jacobl423/F91_Jepler/.agents/teamwork/challenger_m1_1/progress.md

# Progress — Challenger M1-1

Last visited: 2026-10-05T20:36:00Z
Status: Empirical challenge complete. Critical bug identified and reproduced. Verdict: REJECT.

## Completed Milestones & Actions
1. Read ORIGINAL_REQUEST.md, PROJECT.md, DISPATCH.md, and worker_m1/handoff.md.
2. Verified clean build of `Software/macOS_App` with `swift build`.
3. Created empirical stress test harness (`Software/macOS_App/scripts/empirical_challenger_harness.swift`).
4. Verified valid repository binaries (`app.signed.bin`, `mcuboot.elf`, `f91_jepler.resc`, `f91_jepler.kicad_pcb`, `blaster_6810.hex`).
5. Verified 0-byte empty files, corrupted MCUboot headers, corrupted ELF headers, corrupted KiCad PCB S-expressions, directory handling, permissions, and concurrency.
6. Empirically discovered and confirmed CRITICAL SIGTRAP crash (`Fatal error: String index is out of bounds`) in `AssetInspector.swift:344` and `AssetInspector.swift:350` when parsing adversarial pseudo-hex lines with record types 04 and 05.
7. Confirmed that persistent `UserDefaults` state triggers an unrecoverable crash loop on startup.
8. Authored comprehensive adversarial challenge report and handoff in `handoff.md`.
