jacobl423/F91_Jepler/.agents/teamwork/challenger_m2_2/progress.md

# Progress — Challenger M2-2

Last visited: 2026-10-05T21:40:20Z

## Current Status
- Created and executed empirical test harness: `Software/macOS_App/scripts/empirical_challenger_m2_2_harness.swift`.
- Tested 45 empirical test cases across 5 test suites:
  1. Suite 1: Sidebar Visibility Persistence & Dual-Key Synchronization (6 tests, 3 failed)
  2. Suite 2: Sidebar Width Bounds & Clamping 230..380 (8 tests, 4 failed)
  3. Suite 3: Asset Revert Safety (3 tests, all passed)
  4. Suite 4: Non-Modal Action Safety (6 tests, all passed)
  5. Suite 5: ViewMode & Multi-Launch Simulated Cycles (10 tests, all passed)
- Overall Empirical Results: 38 Passed, 7 Failed.
- Final Verdict: REJECT.
- Next: Update BRIEFING.md and write handoff.md.
