jacobl423/F91_Jepler/.agents/teamwork/explorer_m1_1/BRIEFING.md

# BRIEFING — 2026-10-05T20:15:15Z

## Mission
Investigate and specify SessionAsset.swift and AssetInspector.swift for Milestone 1 of the F91_Jepler macOS companion app.

## 🔒 My Identity
- Archetype: explorer
- Roles: Asset Model & Inspector Explorer
- Working directory: /Users/jacobloesch/Documents/F91_Jepler/.agents/teamwork/explorer_m1_1
- Original parent: 6b5ed2d8-2b1d-40f1-8ab6-ad53a69017cd
- Milestone: M1 (Asset Models, Metadata Engine & Session Integration)

## 🔒 Key Constraints
- Read-only investigation — do NOT implement
- Do not modify source code in Software/macOS_App
- Write findings and handoff report to /Users/jacobloesch/Documents/F91_Jepler/.agents/teamwork/explorer_m1_1/handoff.md
- Adhere to Swift 5/6 concurrency, Sendable, @MainActor conventions for macOS 13+

## Current Parent
- Conversation ID: 6b5ed2d8-2b1d-40f1-8ab6-ad53a69017cd
- Updated: not yet

## Investigation State
- **Explored paths**:
  - `ORIGINAL_REQUEST.md`, `PROJECT.md`, `DISPATCH.md`
  - `Software/macOS_App/Package.swift` (macOS 13+, Swift 5.9 tools version)
  - `Software/macOS_App/F91JeplerEmulator/Models/EmulatorSession.swift`
  - `Software/macOS_App/F91JeplerEmulator/Engine/ResourceLoader.swift`
  - `Software/macOS_App/F91JeplerEmulator/Engine/RenodeScriptGenerator.swift`
  - `Software/macOS_App/F91JeplerEmulator/Engine/RenodeProcessManager.swift`
  - `Software/macOS_App/F91JeplerEmulator/Engine/KiCadParser.swift`
  - `Software/macOS_App/F91JeplerEmulator/Views/ContentView.swift`
  - Embedded sample files: `app.signed.bin`, `mcuboot.elf`, `f91_jepler.resc`, `f91_jepler.kicad_pcb`, `blaster_6810.hex`
- **Key findings**:
  - MCUboot image binary header starts with LE magic `0x96F3B83D`, image size at offset 12, semantic version at offset 20.
  - ELF32 ARM binary starts with `\x7fELF`, `EI_CLASS=1`, `EI_DATA=1`, `e_machine=0x0028` (EM_ARM Cortex-M), entry point at offset 24 (with Thumb mode bit).
  - Intel HEX records start with `:`, but Renode `.resc` scripts also have headers `:name:` and `:description:`. Disambiguation requires verifying that payload characters are exclusively hex digits `[0-9a-fA-F]` and record types are `0x00...0x05`.
  - KiCad PCB S-expression starts with `(kicad_pcb`, with regex extraction for `version`, `generator`, and `thickness`.
  - Dynamic binary loading requires generating `sysbus LoadELF`, `sysbus LoadHEX`, or `sysbus LoadBinary ... 0x0c000` based on file extension, and preserving staged file extensions in `RenodeProcessManager`.
  - Hot in-memory PCB reloading updates `pcbBoard` and restarts `pcbFileWatcher` without stopping the running Renode process.
  - Swift concurrency safety: `SessionAssetKind`, `AssetLoadState`, `AssetMetadata`, and `SessionAsset` conform to `Sendable`. `AssetInspector` executes asynchronous non-blocking file I/O on background cooperative threads using `Task.detached`. `EmulatorSession` runs strictly on `@MainActor`.
- **Unexplored areas**:
  - Milestone 2 UI components (`ProjectSidebarView.swift`) and toolbar button integrations (assigned to M2).

## Key Decisions Made
- Validated complete proposed implementations of `proposed_SessionAsset.swift` and `proposed_AssetInspector.swift` against all real repository binaries using native Swift compilation.
- Designed exact interface contracts and backward-compatibility bindings for `EmulatorSession`, `RenodeScriptGenerator`, and `RenodeProcessManager`.

## Artifact Index
- `DISPATCH.md` — Initial dispatch instructions & incoming message log
- `BRIEFING.md` — Working memory state
- `progress.md` — Liveness heartbeat
- `proposed_SessionAsset.swift` — Turnkey Swift model code for `SessionAsset.swift`
- `proposed_AssetInspector.swift` — Turnkey Swift engine code for `AssetInspector.swift`
- `proposed_EmulatorSession_integration.md` — Integration specification and code for `EmulatorSession.swift`
- `proposed_Renode_Binary_Loading.md` — Dynamic binary loading spec for `RenodeScriptGenerator.swift` and `RenodeProcessManager.swift`
- `handoff.md` — Authoritative 5-component handoff report
