jacobl423/F91_Jepler/.agents/teamwork/explorer_m1_1/DISPATCH.md

# Dispatch for Explorer M1_1

## Identity
- Role: Asset Model & Inspector Explorer
- Type: teamwork_preview_explorer
- Working directory: /Users/jacobloesch/Documents/F91_Jepler/.agents/teamwork/explorer_m1_1
- Parent Orchestrator: /Users/jacobloesch/Documents/F91_Jepler/.agents/teamwork/orchestrator_macos
- Authoritative User Request: /Users/jacobloesch/Documents/F91_Jepler/.agents/teamwork/ORIGINAL_REQUEST.md
- Project Scope Document: /Users/jacobloesch/Documents/F91_Jepler/.agents/teamwork/orchestrator_macos/PROJECT.md

## Milestone Scope: M1 - Asset Models & Metadata Engine
Analyze the detailed implementation requirements for:
1. `SessionAsset.swift`: Design `SessionAssetKind` (`.pcb`, `.appFirmware`, `.bootloader`, `.rescScript`), `AssetLoadState`, `AssetMetadata`, and `SessionAsset`.
2. `AssetInspector.swift`: Asynchronous metadata extractor capable of parsing file sizes, modification dates, and binary magic bytes (MCUboot image magic `0x96F3B83D`, ELF32 ARM Cortex-M header `0x7F 'E' 'L' 'F'`, Intel HEX, KiCad S-expression).
3. Recommend exact type signatures, Swift concurrency safety (@MainActor / Sendable), and file structure for `Software/macOS_App/F91JeplerEmulator/Models/SessionAsset.swift` and `Software/macOS_App/F91JeplerEmulator/Engine/AssetInspector.swift`.
4. Write your comprehensive analysis and implementation recommendation to `/Users/jacobloesch/Documents/F91_Jepler/.agents/teamwork/explorer_m1_1/handoff.md`.

## 2026-10-05T20:07:15Z
You are the Asset Model & Inspector Explorer for Milestone 1 of the F91_Jepler project. Your working directory is /Users/jacobloesch/Documents/F91_Jepler/.agents/teamwork/explorer_m1_1. Read /Users/jacobloesch/Documents/F91_Jepler/.agents/teamwork/ORIGINAL_REQUEST.md, /Users/jacobloesch/Documents/F91_Jepler/.agents/teamwork/orchestrator_macos/PROJECT.md, and /Users/jacobloesch/Documents/F91_Jepler/.agents/teamwork/explorer_m1_1/DISPATCH.md before starting work. Investigate and design the exact specifications for SessionAsset.swift and AssetInspector.swift in Software/macOS_App, including SessionAssetKind, AssetLoadState, AssetMetadata, header magic extraction (MCUboot, ELF ARM Cortex-M, Intel HEX, KiCad S-expr), and thread safety. Write your handoff report to /Users/jacobloesch/Documents/F91_Jepler/.agents/teamwork/explorer_m1_1/handoff.md and report back when complete.
