jacobl423/F91_Jepler/.agents/teamwork/explorer_m1_1/progress.md

# Progress — explorer_m1_1

Last visited: 2026-10-05T20:15:25Z
Current status: Completed investigation, validated models against real files, and prepared 5-component handoff report.

## Steps
- [x] Received dispatch message and initialized BRIEFING.md and DISPATCH.md
- [x] Inspect existing `Software/macOS_App` directory layout and files
- [x] Examine `Package.swift` and compiler/target configuration
- [x] Examine existing `EmulatorSession.swift`, `RenodeScriptGenerator.swift`, `KiCadPcbParser.swift`, etc.
- [x] Investigate header magic formats:
  - MCUboot image header structure and magic (`0x96F3B83D`, version, load address, image size)
  - ELF32 header (ident `\x7fELF`, machine `0x28` ARM Cortex-M, entry point, 32-bit LE)
  - Intel HEX format (colon `:` records, hex character validation, address calculation)
  - KiCad PCB S-expression format (`(kicad_pcb ...)` version, generator, thickness)
  - Renode script (`:name:`, `:description:`, platforms)
- [x] Design type signatures and architecture for `SessionAsset.swift` and `AssetInspector.swift`
- [x] Verify thread safety / Swift concurrency (@MainActor vs Sendable background actor/tasks)
- [x] Compile and test proposed models against real binaries in repository
- [x] Write comprehensive handoff report to `handoff.md`
- [ ] Send completion message to parent orchestrator
