jacobl423/F91_Jepler/.agents/teamwork/explorer_m1_2/BRIEFING.md

# BRIEFING — 2026-10-05T20:14:00Z

## Mission
Investigate and design exact modifications for RenodeScriptGenerator.swift and RenodeProcessManager.swift in Software/macOS_App to dynamically support LoadELF, LoadHEX, and LoadBinary for application and bootloader binaries, preserve file extensions in staging, and verify non-blocking hot PCB reloading.

## 🔒 My Identity
- Archetype: explorer
- Roles: Renode & Process Manager Explorer, Dynamic Loading Explorer
- Working directory: /Users/jacobloesch/Documents/F91_Jepler/.agents/teamwork/explorer_m1_2
- Original parent: 6b5ed2d8-2b1d-40f1-8ab6-ad53a69017cd
- Milestone: Milestone 1 - Dynamic Renode Loading & Staging

## 🔒 Key Constraints
- Read-only investigation — do NOT implement directly in Software/macOS_App source
- Deliver structured handoff report in /Users/jacobloesch/Documents/F91_Jepler/.agents/teamwork/explorer_m1_2/handoff.md
- Use send_message to report back to parent

## Current Parent
- Conversation ID: 6b5ed2d8-2b1d-40f1-8ab6-ad53a69017cd
- Updated: not yet

## Investigation State
- **Explored paths**:
  - `Software/macOS_App/F91JeplerEmulator/Engine/RenodeScriptGenerator.swift`
  - `Software/macOS_App/F91JeplerEmulator/Engine/RenodeProcessManager.swift`
  - `Software/macOS_App/F91JeplerEmulator/Models/EmulatorSession.swift`
  - `Software/macOS_App/F91JeplerEmulator/Engine/PCBValidator.swift`
  - `Software/macOS_App/F91JeplerEmulator/Engine/PCBFileWatcher.swift`
  - `Software/macOS_App/F91JeplerEmulator/Engine/KiCadToolService.swift`
  - `Software/macOS_App/F91JeplerEmulator/Views/KiCadPcbView.swift`
  - `Software/macOS_App/F91JeplerEmulator/Resources/Embedded/f91_jepler.resc`
- **Key findings**:
  - `RenodeScriptGenerator.swift` hardcoded `sysbus LoadELF $mcuboot_bin` and `sysbus LoadBinary $app_bin 0x0c000`.
  - Added `BinaryFormat` enum (`.elf`, `.hex`, `.binary`) and `detectFormat(path:)` inspecting ELF magic (`\x7fELF`) / Intel HEX `:` with extension fallback.
  - Added dynamic load command emission: `sysbus LoadELF`, `sysbus LoadHEX`, or `sysbus LoadBinary $app_bin 0x0c000` / `$mcuboot_bin 0x00000`.
  - `RenodeProcessManager.swift` hardcoded staging destination names `app.signed.bin` and `mcuboot.elf`, discarding original file extensions and formats.
  - Redesigned staging to sanitize filenames while preserving extensions (`app.hex`, `zephyr.elf`, `mcuboot.hex`, `mcuboot.bin`, `app.signed.bin`).
  - Verified PCB hot reload in `EmulatorSession.reloadPCB(fileURL:)`: re-parses KiCad files in-memory via `KiCadParser.parseAsync`, runs 15-rule in-memory DRC via `PCBValidator.validate`, refreshes `runKiCadDRC()` if active, and alerts if GPIO pins drift via `GPIOPinAuditor`. Emulation subprocess `RenodeProcessManager` is NOT stopped or restarted; sockets and logs remain alive.
- **Unexplored areas**: Milestone 3 test target setup and test cases.

## Key Decisions Made
- Authored proposed replacement files `proposed_RenodeScriptGenerator.swift` and `proposed_RenodeProcessManager.swift`.
- Authored unified patch `renode_dynamic_loading.patch`.

## Artifact Index
- /Users/jacobloesch/Documents/F91_Jepler/.agents/teamwork/explorer_m1_2/DISPATCH.md — Dispatch instructions
- /Users/jacobloesch/Documents/F91_Jepler/.agents/teamwork/explorer_m1_2/BRIEFING.md — Persistent memory
- /Users/jacobloesch/Documents/F91_Jepler/.agents/teamwork/explorer_m1_2/progress.md — Liveness heartbeat
- /Users/jacobloesch/Documents/F91_Jepler/.agents/teamwork/explorer_m1_2/proposed_RenodeScriptGenerator.swift — Proposed script generator
- /Users/jacobloesch/Documents/F91_Jepler/.agents/teamwork/explorer_m1_2/proposed_RenodeProcessManager.swift — Proposed process manager
- /Users/jacobloesch/Documents/F91_Jepler/.agents/teamwork/explorer_m1_2/renode_dynamic_loading.patch — Unified patch
- /Users/jacobloesch/Documents/F91_Jepler/.agents/teamwork/explorer_m1_2/handoff.md — Final handoff report
