jacobl423/F91_Jepler/.agents/teamwork/explorer_m1_2/progress.md

# Progress: Explorer M1_2 (Renode Dynamic Loading & Staging)
Last visited: 2026-10-05T20:14:55Z

- [x] Initialized DISPATCH.md, BRIEFING.md, and progress.md
- [x] Read ORIGINAL_REQUEST.md and orchestrator_macos/PROJECT.md
- [x] Inspect existing RenodeScriptGenerator.swift and RenodeProcessManager.swift
- [x] Inspect PCB hot reloading in EmulatorSession, KiCadParser, PCBValidator, KiCadToolService, and KiCadPcbView
- [x] Verify non-blocking subprocess independence of PCB reload
- [x] Design exact modifications and diff strategy
- [x] Authored proposed_RenodeScriptGenerator.swift
- [x] Authored proposed_RenodeProcessManager.swift
- [x] Authored renode_dynamic_loading.patch
- [x] Formulate handoff report to handoff.md
- [x] Send completion message to orchestrator
