jacobl423/F91_Jepler/.agents/teamwork/explorer_survey_2_rep/BRIEFING.md

# BRIEFING — 2026-10-05T20:05:00Z

## Mission
Investigate Software/macOS_App asset models, emulator session configurations, file loaders, metadata extraction, quick actions, UTTypes, and session integration for the collapsible sidebar redesign.

## 🔒 My Identity
- Archetype: explorer
- Roles: Asset & Session Explorer
- Working directory: /Users/jacobloesch/Documents/F91_Jepler/.agents/teamwork/explorer_survey_2_rep
- Original parent: 6b5ed2d8-2b1d-40f1-8ab6-ad53a69017cd
- Milestone: macOS Companion App Redesign - Asset & Session Exploration

## 🔒 Key Constraints
- Read-only investigation — do NOT implement
- Scope: Software/macOS_App asset models, emulator session configuration, file handling, UTTypes, Renode bridge
- Never modify source code in Software/macOS_App directly; deliver findings via handoff.md in our agent directory

## Current Parent
- Conversation ID: 6b5ed2d8-2b1d-40f1-8ab6-ad53a69017cd
- Updated: 2026-10-05T19:58:30Z

## Investigation State
- **Explored paths**: Software/macOS_App (EmulatorSession.swift, ResourceLoader.swift, RenodeProcessManager.swift, RenodeScriptGenerator.swift, HardwareSetupView.swift, ContentView.swift, KiCadParser.swift, PCBValidator.swift, GPIOPinAuditor.swift, PCBFileWatcher.swift, Embedded resources: app.signed.bin, mcuboot.elf, f91_jepler.kicad_pcb, f91_jepler.resc).
- **Key findings**:
  1. Renode hardcodes `sysbus LoadBinary $app_bin 0x0c000` and `.bin` copying, breaking `.elf` and `.hex` firmware; must be made format-aware.
  2. Verified MCUboot magic `0x96f3b83d` on `app.signed.bin` and ELF32 ARM header on `mcuboot.elf`.
  3. PCB layouts can be hot-reloaded dynamically into the UI without restarting the Renode emulator.
  4. Non-modal quick actions (Browse/Replace via async NSOpenPanel, Clear, Reload, Reveal in Finder) and dedicated per-card dropzones with UTTypes replace modal sheets and window overlays.
  5. State persistence via `UserDefaults` with validation ensures project settings survive app restarts.
- **Unexplored areas**: None for Phase 0 survey.

## Key Decisions Made
- Completed deep architectural survey and produced comprehensive 5-component handoff report.
- Prepared data structures (`SessionAsset`, `SessionAssetKind`, `AssetLoadState`, `AssetMetadata`), metadata inspection engine (`AssetInspector`), and Renode command dispatch adjustments.

## Artifact Index
- /Users/jacobloesch/Documents/F91_Jepler/.agents/teamwork/explorer_survey_2_rep/handoff.md — Final analysis & handoff report
- /Users/jacobloesch/Documents/F91_Jepler/.agents/teamwork/explorer_survey_2_rep/progress.md — Progress heartbeat
- /Users/jacobloesch/Documents/F91_Jepler/.agents/teamwork/explorer_survey_2_rep/DISPATCH.md — Incoming dispatch record
