jacobl423/F91_Jepler/.agents/teamwork/explorer_survey_2_rep/DISPATCH.md

# Dispatch for Asset Session Explorer (Replacement)

## Identity
- Role: Asset & Session Explorer
- Type: teamwork_preview_explorer
- Working directory: /Users/jacobloesch/Documents/F91_Jepler/.agents/teamwork/explorer_survey_2_rep
- Parent Orchestrator: /Users/jacobloesch/Documents/F91_Jepler/.agents/teamwork/orchestrator_macos
- Authoritative User Request: /Users/jacobloesch/Documents/F91_Jepler/.agents/teamwork/ORIGINAL_REQUEST.md

## Mission & Scope
Investigate the data models, session state, and file handling in `Software/macOS_App`:
1. Study the current emulator session configuration, asset models, file loaders, and bindings.
2. Investigate how `.kicad_pcb`, firmware binaries (`.bin`, `.hex`, `.elf`), and `.resc` scripts are currently loaded, stored, validated, and passed to the emulator/Renode or companion tools.
3. Investigate live asset status, metadata extraction (file size, timestamp, path, validity/format, loaded status), and quick actions (browse/replace via NSOpenPanel, clear, reload, reveal in Finder via NSWorkspace).
4. Investigate drag-and-drop UTTypes, drop delegate handlers, and how dropping `.kicad_pcb`, `.bin`, `.hex`, `.elf`, and `.resc` can update active emulator session configuration live without modal sheets.
5. Document exact models, view models, managers, and proposed data flow.
6. Write your comprehensive analysis report to `/Users/jacobloesch/Documents/F91_Jepler/.agents/teamwork/explorer_survey_2_rep/handoff.md`.

## 2026-10-05T19:58:30Z
[Message] timestamp=2026-10-05T19:58:30Z sender=6b5ed2d8-2b1d-40f1-8ab6-ad53a69017cd priority=MESSAGE_PRIORITY_HIGH content=You are the Asset & Session Explorer (Replacement) for the F91_Jepler project. Your working directory is /Users/jacobloesch/Documents/F91_Jepler/.agents/teamwork/explorer_survey_2_rep. Read /Users/jacobloesch/Documents/F91_Jepler/.agents/teamwork/ORIGINAL_REQUEST.md (specifically the latest request dated 2026-10-05T19:52:40Z) and /Users/jacobloesch/Documents/F91_Jepler/.agents/teamwork/explorer_survey_2_rep/DISPATCH.md before starting work. Investigate Software/macOS_App: examine how emulator session configurations, PCB layouts (.kicad_pcb), firmware binaries (.bin/.hex/.elf), and scripts (.resc) are modeled, validated, loaded, and supplied to the Renode emulator session. Analyze how to implement live metadata extraction, quick actions (browse/replace, clear, reload, reveal in Finder), and drag-and-drop UTTypes so uploads immediately update the session configuration without modal sheets. Write your structured findings and handoff report to /Users/jacobloesch/Documents/F91_Jepler/.agents/teamwork/explorer_survey_2_rep/handoff.md and report back when complete.
