jacobl423/F91_Jepler/.agents/teamwork/explorer_survey_3/BRIEFING.md

# BRIEFING — 2026-10-05T15:06:00Z

## Mission
Investigate Software/macOS_App: inspect Package.swift, dependencies, build settings, test suite structure, current swift build / swift test status, file hierarchy, architectural conventions, macOS API constraints, and testing frameworks.

## 🔒 My Identity
- Archetype: explorer
- Roles: Build & Architecture Explorer
- Working directory: /Users/jacobloesch/Documents/F91_Jepler/.agents/teamwork/explorer_survey_3
- Original parent: 6b5ed2d8-2b1d-40f1-8ab6-ad53a69017cd
- Milestone: macOS Companion & Emulator App Build & Architecture Survey

## 🔒 Key Constraints
- Read-only investigation — do NOT implement
- Write only to /Users/jacobloesch/Documents/F91_Jepler/.agents/teamwork/explorer_survey_3/
- Produce structured 5-component handoff report in handoff.md
- Update progress.md for liveness

## Current Parent
- Conversation ID: 6b5ed2d8-2b1d-40f1-8ab6-ad53a69017cd
- Updated: 2026-10-05T15:06:00Z

## Investigation State
- **Explored paths**:
  - `Software/macOS_App/Package.swift`
  - `Software/macOS_App/scripts/build_app.sh`, `archive_app.sh`
  - `Software/macOS_App/F91JeplerEmulator/App.swift`
  - `Software/macOS_App/F91JeplerEmulator/Views/ContentView.swift`, `HardwareSetupView.swift`, `ToolbarControlsView.swift`, `TerminalView.swift`, `KiCadPcbView.swift`, `CasioWatchFrameView.swift`, `AutomatedTestRunnerView.swift`
  - `Software/macOS_App/F91JeplerEmulator/Models/EmulatorSession.swift`, `AutomatedTestModels.swift`
  - `Software/macOS_App/F91JeplerEmulator/Engine/ResourceLoader.swift`, `RenodeProcessManager.swift`, `RenodeScriptGenerator.swift`, `PCBFileWatcher.swift`
  - `Software/macOS_App/F91JeplerEmulator/Utils/KeyboardMonitor.swift`
  - `Software/macOS_App/F91JeplerEmulator/Resources/Embedded/`
- **Key findings**:
  - `swift build` passes cleanly (exit code 0, 28.8s initial build, zero compiler errors).
  - `swift test` fails because no `Tests` target or directory exists in `Package.swift`.
  - App targets macOS 13+ (`.macOS(.v13)`), Swift 5 language mode (`.v5`), pure Apple frameworks with zero third-party SPM dependencies.
  - The UI uses `HSplitView` inside `ContentView` to split the central workbench views from the UART/Renode terminal.
  - Asset configuration is currently performed via modal sheet `HardwareSetupView` or root `.onDrop` on `ContentView`.
  - Adding a collapsible sidebar requires integrating a left pane into `HSplitView` (or outer layout) with dedicated dropzones, metadata display, quick action buttons, keyboard shortcut (⌘0/⌘B), and state persistence via `UserDefaults`.
- **Unexplored areas**: None. Full codebase inventory and build status completely surveyed.

## Key Decisions Made
- Confirmed `swift build` status is healthy.
- Documented testing gap (`swift test` target missing) and recommended SPM testing structure.
- Formulated recommended UI architecture for collapsible sidebar (3-pane `HSplitView` vs outer collapsible panel, UTType drag-and-drop, state persistence).

## Artifact Index
- handoff.md — Comprehensive handoff report for orchestrator and implementer
- progress.md — Liveness heartbeat and investigation progress
- DISPATCH.md — Incoming dispatches and mission scope
