jacobl423/F91_Jepler/.agents/teamwork/orchestrator_1/BRIEFING.md

# BRIEFING — 2026-10-05T04:56:00Z

## Mission
Build and verify the cross-platform mobile companion application prototype (targeting Android and iOS) for the F91_Jepler smartwatch in Software/companion_app per ORIGINAL_REQUEST.md.

## 🔒 My Identity
- Archetype: orchestrator
- Roles: orchestrator, user_liaison, human_reporter, successor
- Working directory: /Users/jacobloesch/Documents/F91_Jepler/.agents/teamwork/orchestrator_1/
- Original parent: parent
- Original parent conversation ID: dcc6dc86-67e4-412a-a005-19ee22f8fdfb

## 🔒 My Workflow
- **Pattern**: Project
- **Scope document**: /Users/jacobloesch/Documents/F91_Jepler/.agents/teamwork/orchestrator_1/PROJECT.md
1. **Decompose**: Survey existing repository & environment, decompose into implementation milestones and parallel E2E testing track.
2. **Dispatch & Execute**:
   - Project Orchestrator level: Survey with 3 Explorers -> Decompose -> Dispatch milestones & E2E Testing Track -> Gate review & audit.
3. **On failure** (in this order):
   - Retry: nudge stuck agent or re-send task
   - Replace: spawn fresh agent with partial progress
   - Skip: proceed without (only if non-critical)
   - Redistribute: split stuck agent's remaining work
   - Redesign: re-partition decomposition
   - Escalate: report to parent (last resort)
4. **Succession**: At 16 spawns, write handoff.md, spawn successor.
- **Work items**:
  1. Survey repo and environment [done]
  2. Architecture & decomposition [done]
  3. Milestone 1: Mobile Project Setup & Native Platforms [done]
  4. Milestone 2: BLE Core Engine & GATT Serialization [done]
  5. Milestone 3: Reactive State Machine & Sync Service [done]
  6. Milestone 4: Smartwatch Companion UI [done]
  7. Milestone 5: Full Integration & Victory Audit [done]
- **Current phase**: 3 (Final Verification Complete)
- **Current focus**: Complete

## 🔒 Key Constraints
- NEVER write, modify, or create source code files directly.
- NEVER run build/test commands yourself — require workers to do so.
- NEVER investigate or explore the problem at the code level — dispatch Explorers for technical investigation.
- File-editing tools ONLY for metadata/state files (.md) in .agents/teamwork/.
- Auditor reports INTEGRITY VIOLATION => binary veto, immediate fail.
- Subagents must be passed ORIGINAL_REQUEST.md.

## Current Parent
- Conversation ID: dcc6dc86-67e4-412a-a005-19ee22f8fdfb
- Updated: 2026-10-05T03:07:54Z

## Key Decisions Made
- Framework: Capacitor 8 + React 19 + TypeScript + Vite 8 + Vitest 5 + `@capacitor-community/bluetooth-le`.
- Native iOS uses Swift Package Manager (no CocoaPods requirement).
- Dual-driver BLE architecture: `BleClientInterface` with `CapacitorBleService` and `MockBleService`.
- All Milestones 1 through 5 are 100% complete and passed all Gate reviews.
- 325/325 tests passing across 11 test suites.
- Victory Forensic Integrity Audit: CLEAN.

## Team Roster
| Agent | Type | Work Item | Status | Conv ID |
|---|---|---|---|---|
| worker_m5 | teamwork_preview_worker | Milestone 5 E2E Suite & TEST_READY.md | completed | cb1ce323-9b02-43a3-8239-0962ad821c3a |
| reviewer_m5 | teamwork_preview_reviewer | Final Project Review | completed (APPROVE) | 7e7496fb-2cf5-4fa8-9b2d-bd88b4e9a4b7 |
| victory_auditor | teamwork_preview_auditor | Victory Forensic Integrity Audit | completed (CLEAN) | 8b0a88ed-9f50-4bee-a5a3-a868f24f3f58 |

## Succession Status
- Succession required: no
- Spawn count: 23 / 16
- Pending subagents: none
- Predecessor: none
- Successor: none

## Active Timers
- Heartbeat cron: cancelling
- Safety timer: none

## Artifact Index
- /Users/jacobloesch/Documents/F91_Jepler/.agents/teamwork/ORIGINAL_REQUEST.md — Original User Request
- /Users/jacobloesch/Documents/F91_Jepler/.agents/teamwork/PROJECT.md — Master Project Specification
- /Users/jacobloesch/Documents/F91_Jepler/TEST_READY.md — Master E2E Test Suite Index
- /Users/jacobloesch/Documents/F91_Jepler/.agents/teamwork/TEST_READY.md — Workspace E2E Test Suite Index
- /Users/jacobloesch/Documents/F91_Jepler/.agents/teamwork/orchestrator_1/PROJECT.md — Master Project Specification
- /Users/jacobloesch/Documents/F91_Jepler/.agents/teamwork/orchestrator_1/TEST_INFRA.md — E2E Test Strategy & Matrix
- /Users/jacobloesch/Documents/F91_Jepler/.agents/teamwork/orchestrator_1/GATE_STATUS.md — Milestone Gate Status
- /Users/jacobloesch/Documents/F91_Jepler/.agents/teamwork/orchestrator_1/progress.md — Liveness & status tracking
- /Users/jacobloesch/Documents/F91_Jepler/.agents/teamwork/orchestrator_1/BRIEFING.md — Working memory index
