jacobl423/F91_Jepler/.agents/teamwork/orchestrator_1/handoff.md

# Orchestrator Soft Handoff — Generation 1 to Generation 2

**Author**: Project Orchestrator (Gen 1)  
**Recipient**: Successor Project Orchestrator (Gen 2)  
**Parent Conversation ID**: `dcc6dc86-67e4-412a-a005-19ee22f8fdfb`  
**Working Directory**: `/Users/jacobloesch/Documents/F91_Jepler/.agents/teamwork/orchestrator_1`  
**Timestamp**: 2026-10-05T04:23:00Z  

---

## 1. Observation & Work Completed
- **Phase 0 (Survey)**: Complete. 3 parallel Explorers investigated firmware GATT sources (`Firmware/zephyr`), host mobile toolchains, and requirements.
- **Phase 1 (Decomposition & Infrastructure)**: Complete. `PROJECT.md` and `TEST_INFRA.md` created with clear architectural boundaries, feature inventory, and 4-tier test specifications.
- **Milestone 1 (Project Setup & Native Mobile Architecture)**: **DONE & GATE PASSED**.
  - `Software/companion_app` established with Capacitor 8 + React 19 + TypeScript + Vite 8 + Vitest 5.
  - Native Android (`android/`) with Bluetooth permissions (`BLUETOOTH_SCAN`, `BLUETOOTH_CONNECT`, `ACCESS_FINE_LOCATION`).
  - Native iOS (`ios/`) with Swift Package Manager and `NSBluetoothAlwaysUsageDescription`.
  - Smoke tests and build/bundle verified.
- **Milestone 2 (BLE Engine & GATT Serialization Core)**: **DONE & GATE PASSED**.
  - `src/ble/gattConstants.ts`: Complete UUIDs, lengths, and constants matching Zephyr firmware.
  - `src/ble/gattSerializer.ts`: Genuine Little-Endian binary serializers for Time (4B uint32), Timezone (2B signed int16), TimeMode (1B uint8), and DST (1B uint8) with strict length validation.
  - `src/ble/bleClientInterface.ts`: Decoupled Hardware Abstraction Layer.
  - `src/ble/mockBleService.ts`: Virtual F91_Jepler smartwatch with live watch clock, GATT DB, and strict ATT error codes (`BT_ATT_ERR_INVALID_OFFSET` 0x07).
  - `src/ble/capacitorBleService.ts`: Production driver wrapping `@capacitor-community/bluetooth-le`.
  - 95 passing tests.
- **Milestone 3 (State Machine & Sequential Sync Service)**: **DONE & GATE PASSED**.
  - `src/state/connectionStateMachine.ts`: 6 states (`DISCONNECTED`, `SCANNING`, `CONNECTING`, `CONNECTED`, `SYNCING`, `ERROR`) and 11 transitions with universal disconnect safety.
  - `src/state/syncService.ts`: Sequential GATT write pipeline (`Time` -> `Timezone` -> `TimeMode` -> `DST`) with link loss and timeout guards.
  - `src/state/useBleConnection.ts`: Unified React 19 hook with dual-driver runtime switching.
  - 166 passing tests across 8 test suites with 0 typecheck errors.

---

## 2. Milestone State
| Milestone | Status | Key Artifacts |
|---|---|---|
| M1: Project Setup & Native Platforms | **DONE** (Gate Passed) | `android/`, `ios/`, `package.json`, `capacitor.config.ts`, `tests/smoke.test.ts` |
| M2: BLE Engine & Serialization | **DONE** (Gate Passed) | `src/ble/*`, `tests/serialization.test.ts`, `tests/mockBleService.test.ts` |
| M3: State Machine & Sync Service | **DONE** (Gate Passed) | `src/state/*`, `tests/stateMachine.test.ts`, `tests/syncService.test.ts` |
| M4: User Interface & Visual Synchronization Panel | **PLANNED** | Next up for Worker M4 |
| M5: Final Verification & Victory Audit | **PLANNED** | Final milestone |

---

## 3. Active Subagents
- None currently active. All 17 spawned subagents have completed and delivered reports.
- Spawn count has reached 17 / 16, triggering this self-succession.

---

## 4. Key Decisions & Technical Constraints
1. **Never Touch Source Code Directly**: You are a DISPATCH-ONLY orchestrator. Always delegate code writing, test writing, and building to subagents (`invoke_subagent`).
2. **Never Run Tests Directly**: Require Workers, Reviewers, Challengers, and Auditors to run `npm test` and `npm run build`.
3. **Dual Driver BLE**: The companion app supports both physical Bluetooth (`CapacitorBleService`) and simulated smartwatch (`MockBleService`). This allows full testing and browser preview (`npm run dev`) without physical hardware.
4. **Firmware Compatibility**: Exact byte layouts: Time (4B LE), Timezone (2B LE), Mode (1B), DST (1B). Any length mismatch triggers ATT error 0x07.
5. **Auditor Gating**: The Forensic Auditor's verdict is a binary veto. If `INTEGRITY VIOLATION`, the milestone fails unconditionally.

---

## 5. Remaining Work (Concrete Next Steps for Successor)
1. **Milestone 4: User Interface & Visual Synchronization Panel**:
   - Dispatch Worker 4 to implement React 19 components in `src/components/`:
     - `DeviceDiscovery.tsx`: Scan button, loading state, discovered devices list with signal/RSSI and connect buttons.
     - `ConnectionStatusBadge.tsx`: Visual badge showing disconnected, scanning, connecting, connected, or error with clear colors and status text.
     - `ClockSyncPanel.tsx`: Dedicated "Sync Watch Time" button, current system time display, timezone/DST preview, visual sync progress (0% -> 100%), and last synced timestamp display.
     - `MockWatchPreview.tsx`: Visual LCD smartwatch emulator preview panel rendering the simulated watch LCD display (time, date, 12/24h, DST indicator) when in simulated mode.
     - `App.tsx`: Main companion app container with responsive mobile card layout, header, driver toggle (Hardware BLE vs Simulated Watch), and error notifications.
     - `tests/uiComponents.test.tsx`: Component tests verifying scanning, connection, and sync UI triggers.
   - Run Gate review for M4 (Reviewer, Challenger, Forensic Auditor).
2. **Milestone 5: Final Verification & Victory Audit**:
   - Run full 4-tier E2E test verification (`tests/e2eIntegration.test.ts`).
   - Verify 100% test pass rate across all suites, clean production build (`npm run build`), native sync (`npx cap copy`).
   - Run Victory Forensic Audit.
   - Report final completion back to parent orchestrator (`dcc6dc86-67e4-412a-a005-19ee22f8fdfb`).

---

## 6. Key Artifacts
- `/Users/jacobloesch/Documents/F91_Jepler/.agents/teamwork/ORIGINAL_REQUEST.md` — Original request
- `/Users/jacobloesch/Documents/F91_Jepler/.agents/teamwork/PROJECT.md` — Master project spec
- `/Users/jacobloesch/Documents/F91_Jepler/.agents/teamwork/orchestrator_1/GATE_STATUS.md` — Gate history
- `/Users/jacobloesch/Documents/F91_Jepler/.agents/teamwork/orchestrator_1/progress.md` — Progress tracker
- `/Users/jacobloesch/Documents/F91_Jepler/.agents/teamwork/orchestrator_1/BRIEFING.md` — Persistent memory
