jacobl423/F91_Jepler/.agents/teamwork/orchestrator_apk/BRIEFING.md

# BRIEFING — 2026-10-05T05:04:15Z

## Mission
Make the F91_Jepler mobile companion app into a sideloadable Android APK, verify the artifact, and provide sideload instructions.

## 🔒 My Identity
- Archetype: orchestrator
- Roles: orchestrator, user_liaison, human_reporter, successor
- Working directory: /Users/jacobloesch/Documents/F91_Jepler/.agents/teamwork/orchestrator_apk
- Original parent: parent
- Original parent conversation ID: dcc6dc86-67e4-412a-a005-19ee22f8fdfb

## 🔒 My Workflow
- **Pattern**: Project Pattern (APK Generation & Verification)
- **Scope document**: /Users/jacobloesch/Documents/F91_Jepler/.agents/teamwork/orchestrator_apk/SCOPE.md
1. **Decompose**: Survey Android build prerequisites, Capacitor sync, Gradle setup, APK build target, and validation criteria.
2. **Dispatch & Execute**: Direct iteration loop (Explorer -> Worker -> Reviewer -> Challenger -> Auditor)
3. **On failure**: Retry -> Replace -> Skip -> Redistribute -> Redesign -> Escalate
4. **Succession**: At 16 spawns, write handoff.md, spawn successor
- **Work items**:
  1. Survey Android build environment & Capacitor sync status [done]
  2. Build sideloadable APK (assembleDebug) [done]
  3. Validate APK artifact (aapt/apkanalyzer/permissions/launchable) & sideload instructions [done]
- **Current phase**: 4
- **Current focus**: Milestone M6 Complete — synthesis and final report

## 🔒 Key Constraints
- NEVER write, modify, or create source code files directly.
- NEVER run build/test commands yourself — require workers to do so.
- NEVER investigate or explore the problem at the code level — dispatch Explorers for technical investigation.
- File edits only for metadata/state files (.md) in .agents/teamwork/
- Audit is a binary veto.

## Current Parent
- Conversation ID: dcc6dc86-67e4-412a-a005-19ee22f8fdfb
- Updated: 2026-10-05T15:53:00Z

## Key Decisions Made
- Debug APK (assembleDebug) is chosen as the primary sideloadable target because it is automatically signed with the standard Android debug keystore and immediately installable/sideloadable on any Android device without external release signing keys.
- Auto-default to hardware BLE driver (`CapacitorBleService`) when `Capacitor.isNativePlatform()` is true, while preserving manual mock driver toggle for web/testing.

## Team Roster
| Agent | Type | Work Item | Status | Conv ID |
|---|---|---|---|---|
| survey_apk_explorer_1 | teamwork_preview_explorer | Survey Android environment & JDK/SDK | completed | c7833433-a809-4700-ba74-654cd8ee663a |
| survey_apk_explorer_2 | teamwork_preview_explorer | Survey web build & Capacitor Android sync | completed | 8b5b06d5-d236-4afa-9781-7e07b41a84c7 |
| survey_apk_spec_miner | teamwork_preview_spec_miner | Survey APK specs, permissions & verification | completed | 8d50c500-1ffa-40d5-afac-ae19446ef70c |
| worker_m6 | teamwork_preview_worker | Build & verify sideloadable Android APK | completed | 116dbcd8-a4ce-4750-88af-7fac9be6b2d8 |
| reviewer_m6_1 | teamwork_preview_reviewer | Independent review 1 of M6 APK | completed | da52c330-f254-452e-977d-5e4257d1dc92 |
| reviewer_m6_2 | teamwork_preview_reviewer | Independent review 2 of M6 APK | completed | 156bf42c-e366-4821-8adf-d922d7258a2b |
| challenger_m6_1 | teamwork_preview_challenger | Empirical challenge 1: archive, dex, signature | completed | d6e8644d-ac2a-400c-ab25-b586cafe0f26 |
| challenger_m6_2 | teamwork_preview_challenger | Empirical challenge 2: runtime compatibility | completed | a19a9064-caf4-4cba-9cd3-e4e8cdc975af |
| auditor_m6 | teamwork_preview_auditor | Forensic integrity audit of M6 APK build | completed | 3ef5aacc-08c8-45d6-90ef-44da08d1cdf5 |

## Succession Status
- Succession required: no
- Spawn count: 9 / 16
- Pending subagents: none
- Predecessor: none
- Successor: not yet spawned

## Active Timers
- Heartbeat cron: 73b327f6-797d-4e99-bde6-8417a8908ff9/task-10 (every 10m)
- Safety timer: none (relying on heartbeat cron + reactive wakeups)

## Artifact Index
- /Users/jacobloesch/Documents/F91_Jepler/.agents/teamwork/ORIGINAL_REQUEST.md — User request
- /Users/jacobloesch/Documents/F91_Jepler/.agents/teamwork/PROJECT.md — Overall project context
- /Users/jacobloesch/Documents/F91_Jepler/.agents/teamwork/orchestrator_apk/DISPATCH.md — Dispatch history
- /Users/jacobloesch/Documents/F91_Jepler/.agents/teamwork/orchestrator_apk/SCOPE.md — M6 scope document
- /Users/jacobloesch/Documents/F91_Jepler/.agents/teamwork/orchestrator_apk/GATE_STATUS.md — Gate status record
- /Users/jacobloesch/Documents/F91_Jepler/Software/companion_app/F91_Jepler-companion-debug.apk — Top-level sideloadable APK
- /Users/jacobloesch/Documents/F91_Jepler/Software/companion_app/android/app/build/outputs/apk/debug/app-debug.apk — AGP output APK
- /Users/jacobloesch/Documents/F91_Jepler/.agents/teamwork/ORIGINAL_REQUEST.md — User request
- /Users/jacobloesch/Documents/F91_Jepler/.agents/teamwork/PROJECT.md — Overall project context
- /Users/jacobloesch/Documents/F91_Jepler/.agents/teamwork/orchestrator_apk/DISPATCH.md — Dispatch history
