jacobl423/F91_Jepler/.agents/teamwork/orchestrator_apk/progress.md

# Progress Tracking — APK Generation & Verification

Last visited: 2026-10-05T05:04:30Z

## Current Status
Last visited: 2026-10-05T15:52:30Z
- [x] Survey Android build environment, Capacitor sync, Gradle configuration, and SDK availability (Completed by 3 survey subagents)
- [x] Plan and decompose APK generation & verification milestones (Milestone M6 defined in SCOPE.md and PROJECT.md)
- [x] Build signed/sideloadable debug APK (`assembleDebug`) (Completed by worker_m6: 327 tests pass, debug APK built and verified)
- [x] Verify APK artifact (package, manifest, BLE permissions, launchable activity, architecture/integrity)
  - Reviewer 1: APPROVE
  - Reviewer 2: APPROVE
- [x] Challenger verification & audit gating
  - Forensic Auditor: CLEAN (verified Dalvik 037 bytecode, v2 signature, zero cheating)
  - Challenger 1: APPROVE (archive integrity, 4-byte zipalign, DEX headers, tamper resistance)
  - Challenger 2: APPROVE (runtime driver matrix, package manager compatibility, intent filters)
  - Gate Result: PASS
- [x] Final reporting & sideloading instructions

## Iteration Status
Current iteration: 1 / 32

## Retrospective Notes
- **What worked**:
  1. Conducting an initial parallel 3-agent survey accurately caught the Groovy/Java 25 bytecode incompatibility (`major version 69`) before build execution, directing the toolchain to the compatible OpenJDK 21 LTS runtime.
  2. The multi-tiered verification with 2 Reviewers, 2 Challengers, and a Forensic Auditor caught critical edge cases: Android 12+ exported activity requirements, multi-version BLE permission models, memory alignment, and offline web asset bundling.
  3. Generating both the standard AGP output (`app/build/outputs/apk/debug/app-debug.apk`) and a convenient project root copy (`F91_Jepler-companion-debug.apk`) simplifies sideloading access for the user.
- **Lessons learned**:
  1. On modern Android (API 31+), `android:exported="true"` is mandatory on `<activity>` elements containing `<intent-filter>`, which must be validated during build reviews.
  2. Debug keystore signing with APK Signature Scheme v2 allows immediate, universal sideloading without complex production key management, but requires clear instructions to the user on navigating the expected Google Play Protect prompt.
