jacobl423/F91_Jepler/.agents/teamwork/reviewer_m4/BRIEFING.md

# BRIEFING — 2026-10-05T04:40:00Z

## Mission
Perform independent quality review and adversarial critique of Milestone 4 (User Interface & Visual Synchronization Panel) in `/Users/jacobloesch/Documents/F91_Jepler/Software/companion_app`.

## 🔒 My Identity
- Archetype: reviewer
- Roles: reviewer, critic
- Working directory: /Users/jacobloesch/Documents/F91_Jepler/.agents/teamwork/reviewer_m4
- Original parent: 597ea6c0-a703-4980-a746-5cc67a9a63e2
- Milestone: Milestone 4
- Instance: 1 of 1

## 🔒 Key Constraints
- Review-only — do NOT modify implementation code
- Check for integrity violations (hardcoding, facades, shortcuts, fake verification)
- Run independent verification: npm test, npm run typecheck, npm run build
- Adversarial challenge: stress-test assumptions, failure modes, edge cases

## Current Parent
- Conversation ID: 597ea6c0-a703-4980-a746-5cc67a9a63e2
- Updated: 2026-10-05T04:40:00Z

## Review Scope
- **Files to review**: `src/components/DeviceDiscovery.tsx`, `src/components/ConnectionStatusBadge.tsx`, `src/components/ClockSyncPanel.tsx`, `src/components/MockWatchPreview.tsx`, `src/App.tsx`, `src/App.css`, `tests/uiComponents.test.tsx`, `tests/challenge_m4.test.tsx`
- **Interface contracts**: `PROJECT.md`, `ORIGINAL_REQUEST.md`, `worker_m4/handoff.md`
- **Review criteria**: correctness, style, conformance, integrity, robustness

## Review Checklist
- **Items reviewed**:
  - `src/components/ConnectionStatusBadge.tsx`: Confirmed all 6 FSM states, icons, ARIA attributes, RSSI and device readouts
  - `src/components/DeviceDiscovery.tsx`: Confirmed scan triggers, stop scan, empty state, RSSI signal tiers, connect/disconnect buttons
  - `src/components/ClockSyncPanel.tsx`: Confirmed 1s interval clock, 12h/24h toggle, DST toggle, manual sync button, progress bar, last synced timestamp
  - `src/components/MockWatchPreview.tsx`: Confirmed authentic Casio F-91W LCD styling, polling virtual registers, time/date UTC math, AM/PM formatting
  - `src/App.tsx` & `src/App.css`: Confirmed mobile layout, safe-area insets, driver switcher, dismissible error alerts
  - `tests/uiComponents.test.tsx`: 27 passing tests
  - `tests/challenge_m4.test.tsx`: 30 passing adversarial stress tests
- **Verdict**: APPROVE
- **Unverified claims**: none; all claims verified independently via test runner and build pipeline

## Attack Surface
- **Hypotheses tested**:
  - H1: Memory leaks from interval timers in ClockSyncPanel & MockWatchPreview on unmount -> PASS (clearInterval called)
  - H2: Midnight and Noon 12H formatting anomalies (12:00 AM vs 12:00 PM) -> PASS (12 AM/PM correct)
  - H3: Rollover across day and date boundaries with negative and positive timezone offsets -> PASS (UTC math correct)
  - H4: Signal quality categorization boundary conditions (>= -60, -72, -85) -> PASS (correctly categorized)
  - H5: Mid-sync user disruption (disconnect button disabled during SYNCING) -> PASS (guarded)
- **Vulnerabilities found**: No blocker vulnerabilities found; minor observation on driver swapping while scan in-flight (auto-aborts on timeout)
- **Untested angles**: Hardware BLE testing on physical Android/iOS silicon (simulated in Vitest environment)

## Key Decisions Made
- Confirmed zero integrity violations (no hardcoding, facades, or shortcut bypasses)
- Confirmed 100% test pass rate across 10 test files and 223 tests
- Issued APPROVE verdict for Milestone 4

## Artifact Index
- handoff.md — Reviewer verdict and handoff report
- progress.md — Heartbeat and activity log
- DISPATCH.md — Incoming directives log
