jacobl423/F91_Jepler/.agents/teamwork/reviewer_m4/handoff.md

# Handoff Report: Milestone 4 Independent Quality & Adversarial Review

**Author**: Reviewer M4 (Reviewer & Critic)  
**Recipient**: Orchestrator (`597ea6c0-a703-4980-a746-5cc67a9a63e2`)  
**Target Milestone**: Milestone 4 — User Interface & Visual Synchronization Panel  
**Workspace**: `/Users/jacobloesch/Documents/F91_Jepler/Software/companion_app`  
**Verdict**: **APPROVE**  
**Timestamp**: 2026-10-05T04:41:00Z  

---

## 1. Observation

### 1.1 Scope and Specification Baseline
- **Files under review**:
  - `src/components/ConnectionStatusBadge.tsx` (132 lines)
  - `src/components/DeviceDiscovery.tsx` (236 lines)
  - `src/components/ClockSyncPanel.tsx` (296 lines)
  - `src/components/MockWatchPreview.tsx` (249 lines)
  - `src/App.tsx` (208 lines)
  - `src/App.css` (57 lines)
  - `tests/uiComponents.test.tsx` (560 lines)
  - `tests/challenge_m4.test.tsx` (328 lines)
- **Requirement Reference**: `ORIGINAL_REQUEST.md` §R4 (lines 30-32):
  > "Provide a mobile user interface allowing users to scan for nearby watches, inspect found devices, initiate connect/disconnect actions, observe live connection status, and trigger manual time synchronization via a dedicated button with visual feedback."

### 1.2 Direct Inspection of Deliverables
1. **`ConnectionStatusBadge.tsx`**:
   - Implements full mapping for all 6 FSM states: `DISCONNECTED`, `SCANNING`, `CONNECTING`, `CONNECTED`, `SYNCING`, `ERROR`.
   - Distinct color treatments and animations: Sky pulse for scanning, amber spin for connecting, emerald static for connected, indigo spin for syncing, rose alert for error, slate for disconnected.
   - Live peripheral details: device ID truncation and RSSI readout (`device.rssi dBm`).
   - Accessible roles: Container declares `role="status"` and `aria-live="polite"`.
2. **`DeviceDiscovery.tsx`**:
   - Header with scan control button toggling between "Scan for Watches" and "Stop Scan" (animated spinner).
   - Filter display confirming Clock Service UUID `fa35b2f0...`.
   - Signal quality calculator (`getSignalQuality`):
     - `rssi >= -60`: Excellent (4 bars, `text-emerald-400`)
     - `rssi >= -72`: Good (3 bars, `text-teal-400`)
     - `rssi >= -85`: Fair (2 bars, `text-amber-400`)
     - `< -85`: Weak (1 bar, `text-rose-400`)
     - `undefined`: Unknown (0 bars, `text-slate-500`)
   - Empty state messaging for both idle and active scanning phases.
   - Context-aware action buttons: Connect (with loading indicator), Connected tag, and Disconnect button.
   - Buttons correctly disabled during busy states (`CONNECTING`, `SYNCING`).
3. **`ClockSyncPanel.tsx`**:
   - Digital clock ticking every 1000ms with formatted weekday, month, day, year.
   - System timezone identifier and calculated offset string (e.g., `UTC-05:00`).
   - Interactive 12H / 24H button group.
   - Daylight Saving Time (DST) auto-detection (`detectSystemDst`) with interactive override toggle.
   - Dedicated "Sync Watch Time" button disabled when disconnected or actively syncing.
   - Animated GATT write pipeline progress bar tracking step (`TIME`, `TIMEZONE`, `TIMEMODE`, `DST`, `COMPLETED`) and percent (0% to 100%).
   - "Last Synced" timestamp display and duration / write confirmation readout.
4. **`MockWatchPreview.tsx`**:
   - Authentic Casio F-91W resin watch case styling with side pushers ("LIGHT", "MODE", "ALARM / 24HR").
   - Classic bezel typography ("CASIO", "WATER RESIST", "F-91W", "ALARM CHRONOGRAPH").
   - Olive-green LCD display (`#9ea78e`) with day-of-week, day-of-month, 24H/PM mode indicator, digital hours:minutes, seconds, DST indicator, and BLE link icon.
   - Live synchronization with `MockBleService.getWatchState()`, reflecting internal simulated registers (`clockTime`, `clockTimezone`, `clockTimeMode`, `clockDst`).
   - Fallback rendering when running with `CapacitorBleService` (labels as "Hardware Driver").
5. **`App.tsx` & `App.css`**:
   - Mobile-optimized layout with safe-area insets (`env(safe-area-inset-top)` / `bottom` / `left` / `right`).
   - Driver switcher toggling between "Simulated Watch" and "Hardware BLE".
   - Dismissible error banner for Bluetooth or GATT write errors.

### 1.3 Independent Tool Execution Results
1. **Unit & Integration Tests**:
   - Command: `npm test`
   - Output:
     ```
     Test Files  10 passed (10)
          Tests  223 passed (223)
       Duration  1.29s
     ```
   - All 10 test suites passed 100%:
     - `serialization.test.ts`: 20/20 passed
     - `mockBleService.test.ts`: 25/25 passed
     - `syncService.test.ts`: 14/14 passed
     - `stateMachine.test.ts`: 39/39 passed
     - `smoke.test.ts`: 6/6 passed
     - `uiComponents.test.tsx`: 27/27 passed
     - `challenge_m1.test.ts`: 16/16 passed
     - `challenge_m2.test.ts`: 28/28 passed
     - `challenge_m3.test.ts`: 18/18 passed
     - `challenge_m4.test.tsx`: 30/30 passed
2. **TypeScript Strict Typecheck**:
   - Command: `npm run typecheck` (`tsc --noEmit`)
   - Output: Exited with code 0 and zero diagnostic errors.
3. **Production Build**:
   - Command: `npm run build` (`tsc && vite build`)
   - Output:
     ```
     ✓ built in 325ms
     dist/index.html                   0.53 kB │ gzip:  0.34 kB
     dist/assets/index-_qkASCwR.css   22.89 kB │ gzip:  5.27 kB
     dist/assets/web-xfd1Qzza.js       7.64 kB │ gzip:  2.22 kB
     dist/assets/index-SKErwit8.js   294.37 kB │ gzip: 88.43 kB
     ```

### 1.4 Forensic Integrity Checks
- **Hardcoded outputs in source**: None found. Values are dynamically calculated from `new Date()` or simulated registers.
- **Dummy/Facade implementations**: None found. Full interactive state management, timers, and callbacks are wired to `useBleConnection`.
- **Shortcuts or task bypasses**: None found. Follows all design criteria from `ORIGINAL_REQUEST.md` and `PROJECT.md`.
- **Fabricated verification outputs**: None found. All test runs were executed independently and confirmed.

---

## 2. Logic Chain

1. **Requirement Satisfaction (§R4)**:
   - Observation 1.1 requires scanning for nearby watches, inspecting devices, connect/disconnect controls, observing connection state, and manual sync with visual feedback.
   - Observation 1.2 confirms `DeviceDiscovery.tsx` provides scanning triggers, filtering, device listing, and connect/disconnect buttons.
   - Observation 1.2 confirms `ConnectionStatusBadge.tsx` provides distinct live indicators across all 6 machine states.
   - Observation 1.2 confirms `ClockSyncPanel.tsx` provides the manual sync button with step progress bar and last-synced timestamp.
   - Therefore, Requirement R4 and all related acceptance criteria are completely satisfied.

2. **Adversarial Stress Testing & Robustness**:
   - `challenge_m4.test.tsx` stress-tested the UI against boundary conditions:
     - Boundary RSSI values (-60, -72, -85 dBm) verified correct categorization.
     - Mid-sync protection verified: Disconnect button is disabled while `status === 'SYNCING'` to prevent mid-sync aborts.
     - Timer cleanup verified: Both `ClockSyncPanel` and `MockWatchPreview` clean up their `setInterval` handlers on unmount.
     - Midnight and noon 12H formatting verified: 00:00 UTC renders `12:00 AM`, 12:00 UTC renders `12:00 PM`.
     - Date and day-of-week rollovers across midnight with positive and negative timezone offsets verified.
     - Rapid consecutive mount/unmount cycles (50 iterations) executed without leaking intervals or throwing memory errors.
   - Therefore, the implementation is robust under stress.

3. **Build and Test Verification**:
   - Observation 1.3 confirms 100% test pass rate across 223 tests (10 test suites), 0 TypeScript compiler errors, and successful production bundle compilation.
   - Therefore, the codebase maintains strict structural and runtime health.

---

## 3. Caveats

1. In `MockWatchPreview.tsx`, live register inspection is only available when using `MockBleService`. When connected to `CapacitorBleService` (live mobile hardware), raw GATT registers are not exposed over BLE read without active notifications enabled on the firmware. The preview reflects this by displaying "Hardware Driver".
2. When switching drivers via `App.tsx` while an active scan is running, the scan timer in `useBleConnection` will auto-stop the scan after 15 seconds; starting a fresh scan immediately clears the old timer.

---

## 4. Conclusion

**Verdict: APPROVE**

Milestone 4 (User Interface & Visual Synchronization Panel) has been thoroughly verified, stress-tested, and audited. The implementation is genuine, complete, accessible, conforms strictly to all project specifications, and passes 100% of automated tests with zero typecheck or build errors. No integrity violations or blocking flaws were detected.

The project is ready to proceed to Milestone 5.

---

## 5. Verification Method

To independently reproduce and verify this review:

1. **Run Full Test Suite**:
   ```bash
   cd /Users/jacobloesch/Documents/F91_Jepler/Software/companion_app
   npm test
   ```
   *Expected Result*: 10 test files passed, 223/223 tests passed (100%).

2. **Run Strict TypeScript Typecheck**:
   ```bash
   cd /Users/jacobloesch/Documents/F91_Jepler/Software/companion_app
   npm run typecheck
   ```
   *Expected Result*: Exits with code 0 and zero errors.

3. **Run Production Bundle Build**:
   ```bash
   cd /Users/jacobloesch/Documents/F91_Jepler/Software/companion_app
   npm run build
   ```
   *Expected Result*: Exits with code 0, bundling clean assets into `dist/`.
