jacobl423/F91_Jepler/.agents/teamwork/reviewer_m4/progress.md

# Progress Log — Reviewer M4

- Last visited: 2026-10-05T04:40:00Z
- Status: Review and adversarial audit completed.
- Current Step: Generating handoff report (handoff.md) and notifying orchestrator.
- Verdict: APPROVE.
