jacobl423/F91_Jepler/.agents/teamwork/survey_apk_explorer_1/progress.md

# Progress

Last visited: 2026-10-05T05:13:30Z
Current Status: Survey complete. handoff.md written. Message sent to parent.

- [x] Initialized DISPATCH.md and BRIEFING.md
- [x] Survey Java / JDK installations & JAVA_HOME (identified JDK 21, 25, 27; tested Gradle compatibility)
- [x] Survey Android SDK, build tools, platforms, cmdline-tools (identified SDK path, licenses, installed platforms 33, 34, 36)
- [x] Survey Android project configuration (`Software/companion_app/android`, Gradle 8.14.3, AGP 8.13, Capacitor 8)
- [x] Test Gradle execution readiness / dry run & assembleDebug verified
- [x] Synthesize findings and write handoff.md
- [x] Send handoff message to parent
