jacobl423/F91_Jepler/.agents/teamwork/survey_apk_explorer_2/progress.md

# Progress — survey_apk_explorer_2

- Last visited: 2026-10-05T05:10:30Z
- Status: Investigation completed, drafting handoff.md.
- Completed:
  - Investigated `Software/companion_app` web build configs (`package.json`, `vite.config.ts`, `capacitor.config.ts`).
  - Tested `npm run build` and inspected `dist/` artifacts.
  - Tested `npx cap sync android` and inspected asset synchronization into `android/app/src/main/assets/public`.
  - Investigated native plugin integration (`@capacitor-community/bluetooth-le` linking in Gradle, `capacitor.plugins.json`, `MainActivity.java`, `AndroidManifest.xml`).
  - Identified Gradle invocation prerequisites and environment blockers (lack of Java in PATH, Java 25 class version 69 incompatibility with Gradle 8.14.3, JDK 21 installation requirement, compileSdkVersion 36 vs installed platform 34).
- Next steps:
  - Write `handoff.md` with complete 5-component report.
  - Send message back to parent agent.
