jacobl423/F91_Jepler/.agents/teamwork/survey_explorer_2/BRIEFING.md

# BRIEFING — 2026-10-05T03:10:00Z

## Mission
Survey host development environment and evaluate cross-platform mobile frameworks for F91_Jepler companion app in Software/companion_app.

## 🔒 My Identity
- Archetype: explorer
- Roles: Tech Stack & Environment Explorer
- Working directory: /Users/jacobloesch/Documents/F91_Jepler/.agents/teamwork/survey_explorer_2
- Original parent: 597ea6c0-a703-4980-a746-5cc67a9a63e2
- Milestone: exploration

## 🔒 Key Constraints
- Read-only investigation — do NOT implement
- Inspect host environment (Node, npm, toolchains, mobile frameworks)
- Evaluate Android & iOS cross-platform frameworks for BLE support, clean build/bundle, and testability
- Recommend exact framework, directory structure, package manager, and build/test commands

## Current Parent
- Conversation ID: 597ea6c0-a703-4980-a746-5cc67a9a63e2
- Updated: 2026-10-05T03:10:00Z

## Investigation State
- **Explored paths**:
  - `/Users/jacobloesch/Documents/F91_Jepler/Software`
  - `/Users/jacobloesch/Documents/F91_Jepler/.agents/teamwork/ORIGINAL_REQUEST.md`
  - System toolchains: Node v26.10.0, npm 11.19.1, Git 2.55.0, Android Studio at `/Applications/Android Studio.app` (JBR Java 25.0.3), Android SDK at `~/Library/Android/sdk` (API 33, 34), Xcode 27.0 at `/Applications/Xcode.app`
  - Benchmark sandbox at `/tmp/test_cap` (Vite 8, Vitest 5, Capacitor 8, @capacitor-community/bluetooth-le 8.3.0)
- **Key findings**:
  - Node v26.10.0 & npm 11.19.1 operate without friction.
  - Xcode 27.0 license is unaccepted (requires sudo / interactive shell); CocoaPods is missing.
  - System Java is unlinked; Android Studio JBR Java 25 is present.
  - Capacitor 8 generates native Android & iOS platforms with Swift Package Manager (no CocoaPods needed).
  - Bundling with `vite build` completes in <2s and `npx cap copy` syncs to native shells in 8ms.
  - Automated tests run via Vitest in ~140ms in pure Node without physical devices.
- **Unexplored areas**:
  - None within Explorer 2 scope. Implementation phase will execute scaffolding.

## Key Decisions Made
- [Initial] Explored toolchain limits across React Native, Expo, Flutter, and Capacitor.
- [Final Decision] Formally recommend Capacitor 8 + React 19 + TypeScript + Vite 8 + Vitest 5 + @capacitor-community/bluetooth-le. Dual-driver BLE architecture (CapacitorBleService + MockBleService).

## Artifact Index
- `.agents/teamwork/survey_explorer_2/DISPATCH.md` — Assigned task instructions
- `.agents/teamwork/survey_explorer_2/BRIEFING.md` — Persistent working memory
- `.agents/teamwork/survey_explorer_2/progress.md` — Liveness heartbeat
- `.agents/teamwork/survey_explorer_2/handoff.md` — Final survey report
