jacobl423/F91_Jepler/.agents/teamwork/survey_explorer_2/DISPATCH.md

# Dispatch to Survey Explorer 2 (Environment & Mobile Tech Stack Explorer)

## Objective
Investigate the system development environment and `/Users/jacobloesch/Documents/F91_Jepler/Software/companion_app` to determine the most viable, robust, and clean cross-platform mobile project architecture targeting Android and iOS, with seamless mock BLE testing and bundle capabilities.

## References
- Original User Request: `/Users/jacobloesch/Documents/F91_Jepler/.agents/teamwork/ORIGINAL_REQUEST.md`

## Instructions
1. Read `/Users/jacobloesch/Documents/F91_Jepler/.agents/teamwork/ORIGINAL_REQUEST.md`.
2. Inspect the current directory contents of `/Users/jacobloesch/Documents/F91_Jepler/Software/companion_app` and existing toolchains (node, npm, pnpm, yarn, react-native, flutter, etc.) in the environment.
3. Evaluate framework options (e.g. React Native / Expo, Flutter, Ionic/Capacitor, or Web/PWA-ready cross-platform framework) for:
   - Clean setup within `Software/companion_app`
   - Android & iOS targeting capability
   - BLE integration feasibility and mock BLE abstraction
   - Automated testing and bundling without requiring physical devices
4. Recommend the exact framework, directory structure, package manager, and build/test commands.
5. Output your findings as a comprehensive report at `/Users/jacobloesch/Documents/F91_Jepler/.agents/teamwork/survey_explorer_2/handoff.md`.

## 2026-10-05T03:08:48Z
You are Survey Explorer 2 (Tech Stack & Environment Explorer).
Your task is defined in `/Users/jacobloesch/Documents/F91_Jepler/.agents/teamwork/survey_explorer_2/DISPATCH.md`.
Read `/Users/jacobloesch/Documents/F91_Jepler/.agents/teamwork/ORIGINAL_REQUEST.md`, inspect `/Users/jacobloesch/Documents/F91_Jepler/Software/companion_app` and the host environment (Node, npm, toolchains, mobile frameworks).
Evaluate cross-platform mobile frameworks for Android/iOS capability, clean build/bundle, BLE support, and testability.
Recommend the exact framework, directory structure, package manager, and build/test commands.
Write your complete report to `/Users/jacobloesch/Documents/F91_Jepler/.agents/teamwork/survey_explorer_2/handoff.md` and send a summary message back when done.
