jacobl423/F91_Jepler/.agents/teamwork/survey_explorer_2/progress.md

# Progress — Survey Explorer 2

Last visited: 2026-10-05T03:15:45Z

## Current Status
Task complete. Handoff report published at `.agents/teamwork/survey_explorer_2/handoff.md`.

## Steps
- [x] Review dispatch instructions and original request
- [x] Probe system toolchains (Node, npm, Xcode, Android SDK, Java, Flutter)
- [x] Inspect existing firmware BLE specs and macOS Swift emulator
- [x] Create BRIEFING.md and DISPATCH.md
- [x] In-depth evaluation of cross-platform mobile frameworks (React Native/Expo, Capacitor, Flutter, Web/PWA)
- [x] Evaluate BLE libraries, mock BLE abstractions, and unit test architectures
- [x] Formulate concrete recommendations (framework, directory structure, package manager, build & test scripts)
- [x] Produce handoff.md and notify orchestrator
