jacobl423/F91_Jepler/.agents/teamwork/survey_explorer_3/DISPATCH.md

# Dispatch to Survey Explorer 3 (Requirements & E2E Testing Strategy Explorer)

## Objective
Map out complete functional requirements, state machine transitions, GATT sync workflows, UI requirements, and end-to-end testing strategy based on `ORIGINAL_REQUEST.md`.

## References
- Original User Request: `/Users/jacobloesch/Documents/F91_Jepler/.agents/teamwork/ORIGINAL_REQUEST.md`

## Instructions
1. Read `/Users/jacobloesch/Documents/F91_Jepler/.agents/teamwork/ORIGINAL_REQUEST.md`.
2. Enumerate all features, constraints, error conditions, edge cases, and test vectors:
   - Connection state machine states: disconnected, scanning, connecting, connected, error/disconnected
   - GATT characteristics payload layouts and serialization test vectors (epoch seconds uint32 LE, timezone offset uint16 LE, time mode uint8, DST uint8)
   - UI elements and interactions: scan button, device discovery list, connect/disconnect button, connection indicator, manual sync button, visual sync feedback/timestamp
   - Automated testing suite design (unit tests, mock BLE abstraction, state machine tests, serialization tests)
3. Formulate the 4-tier test case hierarchy (Tier 1 Feature, Tier 2 Boundary/Corner, Tier 3 Pairwise, Tier 4 Real-World Workload).
4. Output your findings as a comprehensive report at `/Users/jacobloesch/Documents/F91_Jepler/.agents/teamwork/survey_explorer_3/handoff.md`.

## 2026-10-05T03:08:48Z
You are Survey Explorer 3 (Requirements & Testing Explorer).
Your task is defined in `/Users/jacobloesch/Documents/F91_Jepler/.agents/teamwork/survey_explorer_3/DISPATCH.md`.
Read `/Users/jacobloesch/Documents/F91_Jepler/.agents/teamwork/ORIGINAL_REQUEST.md`.
Enumerate all features, state machine transitions, GATT sync workflows, UI requirements, edge cases, and test vectors. Formulate a 4-tier test case hierarchy.
Write your complete report to `/Users/jacobloesch/Documents/F91_Jepler/.agents/teamwork/survey_explorer_3/handoff.md` and send a summary message back when done.
