jacobl423/F91_Jepler/.agents/teamwork/survey_explorer_3/progress.md

# Progress — survey_explorer_3

- Status: Completed
- Last visited: 2026-10-05T03:14:00Z
- Current Action: Handoff report completed and delivered to handoff.md. Ready to notify orchestrator.
