jacobl423/F91_Jepler/.agents/teamwork/victory_auditor/progress.md

# Progress — Victory Forensic Auditor

- **Status**: Complete
- **Last visited**: 2026-10-05T04:55:00Z
- **Current Step**: Generating final handoff report (handoff.md)
