jacobl423/F91_Jepler/.agents/teamwork/worker_m4/handoff.md

# Handoff Report: Milestone 4 — User Interface & Visual Synchronization Panel

**Author**: Worker 4 (Milestone 4 Implementer)  
**Recipient**: Orchestrator (`597ea6c0-a703-4980-a746-5cc67a9a63e2`)  
**Workspace**: `/Users/jacobloesch/Documents/F91_Jepler/Software/companion_app`  
**Timestamp**: 2026-10-05T04:35:00Z  

---

## 1. Observation

### 1.1 Specification & Assigned Scope Baseline
- **File**: `/Users/jacobloesch/Documents/F91_Jepler/.agents/teamwork/worker_m4/DISPATCH.md` (lines 14-41):
  - Assigned exclusively to Worker 4:
    - `src/components/DeviceDiscovery.tsx`
    - `src/components/ConnectionStatusBadge.tsx`
    - `src/components/ClockSyncPanel.tsx`
    - `src/components/MockWatchPreview.tsx`
    - `src/App.tsx`
    - `src/App.css`
    - `tests/uiComponents.test.tsx`
  - Functional Specifications:
    1. `DeviceDiscovery.tsx`: Scan for nearby watches, inspect found devices (`F91_Jepler`), initiate connect/disconnect actions, observe RSSI/signal strength.
    2. `ConnectionStatusBadge.tsx`: Render live connection state (`disconnected`, `scanning`, `connecting`, `connected`, `syncing`, `error`) with distinct visual indicators and device info.
    3. `ClockSyncPanel.tsx`: Dedicated manual time synchronization button with visual feedback, live local system clock display, timezone offset, 12h/24h toggle, DST status, visual progress bar, and "Last Synced" timestamp display showing successful sync.
    4. `MockWatchPreview.tsx`: Visual F-91W inspired digital LCD display panel reflecting simulated watch registers when using `MockBleService`.
    5. `App.tsx` & `App.css`: Mobile-optimized layout, clean responsive cards, driver toggle between "Hardware BLE" and "Simulated Watch", error alerts.
    6. `tests/uiComponents.test.tsx`: React Testing Library tests verifying scan triggers, device list rendering, connection controls, manual sync button click, and visual sync confirmation.
    7. Clean execution of `npm test`, `npm run typecheck`, and `npm run build` with 100% pass rate.
- **File**: `/Users/jacobloesch/Documents/F91_Jepler/.agents/teamwork/ORIGINAL_REQUEST.md` (lines 30-32):
  - Requirement R4 (Companion User Interface): "Provide a mobile user interface allowing users to scan for nearby watches, inspect found devices, initiate connect/disconnect actions, observe live connection status, and trigger manual time synchronization via a dedicated button with visual feedback."

### 1.2 Implemented Components and Deliverables
The following files were created/modified in `Software/companion_app`:
1. `src/components/ConnectionStatusBadge.tsx` (117 lines):
   - Handles all 6 connection machine states (`DISCONNECTED`, `SCANNING`, `CONNECTING`, `CONNECTED`, `SYNCING`, `ERROR`).
   - Distinct visual states: sky ping animation for scanning, amber spin animation for connecting, emerald glow for connected, indigo spin animation for syncing, rose alert for error, and slate for disconnected.
   - Live peripheral details: device ID and RSSI readout (`-58 dBm`).
   - Accessible ARIA status roles (`role="status"`, `aria-live="polite"`).
2. `src/components/DeviceDiscovery.tsx` (236 lines):
   - Peripheral scan trigger with active scanning indicator and "Stop Scan" button.
   - Discovered devices list with F-91W badge tagging, device ID, and signal quality meter (Excellent/Good/Fair/Weak based on RSSI dBm).
   - Context-sensitive action buttons: "Connect" (with loading state when connecting), "Connected" checkmark indicator, and "Disconnect" trigger.
   - Empty state guidance for both idle and active scanning phases.
3. `src/components/ClockSyncPanel.tsx` (296 lines):
   - Live digital clock ticking every 1000ms with formatted date (`weekday`, `month`, `day`, `year`).
   - System timezone calculation and display (e.g. `UTC-05:00` with system timezone identifier).
   - 12H vs 24H display format toggle button group.
   - Daylight Saving Time (DST) active vs standard indicator and toggle switch.
   - Dedicated "Sync Watch Time" button, disabled when disconnected or actively syncing.
   - Animated GATT write pipeline progress bar tracking step (`TIME`, `TIMEZONE`, `TIMEMODE`, `DST`, `COMPLETED`) and percent (0% to 100%).
   - "Last Synced" timestamp display and duration / write confirmation readout.
4. `src/components/MockWatchPreview.tsx` (228 lines):
   - High-fidelity Casio F-91W resin watch case styling with side pushers ("LIGHT", "MODE", "ALARM / 24HR").
   - Classic bezel typography ("CASIO", "WATER RESIST", "F-91W", "ALARM CHRONOGRAPH").
   - Olive-green LCD digital display (`#9ea78e`) with day-of-week, day-of-month, 24H/PM mode indicator, digital hours:minutes, seconds, DST indicator, and BLE link icon.
   - Live synchronization with `MockBleService.getWatchState()`, reflecting internal simulated registers (`clockTime`, `clockTimezone`, `clockTimeMode`, `clockDst`).
5. `src/App.tsx` (207 lines):
   - Mobile-optimized responsive layout with safe-area insets.
   - Driver toggle switching between "Simulated Watch" (`MockBleService`) and "Hardware BLE" (`CapacitorBleService`).
   - Dismissible error banner for connection or GATT failures.
   - Integration of all three cards (`DeviceDiscovery`, `ClockSyncPanel`, `MockWatchPreview`) driven by `useBleConnection`.
6. `src/App.css` (53 lines):
   - Safe-area insets (`env(safe-area-inset-top)` / `env(safe-area-inset-bottom)`).
   - Monospace LCD font adjustments, radar pulse keyframe animations, glow utilities, and mobile tap highlight suppression.
7. `tests/uiComponents.test.tsx` (412 lines):
   - 27 comprehensive React Testing Library tests covering:
     - `ConnectionStatusBadge` (7 tests): all states, device info, ARIA roles.
     - `DeviceDiscovery` (6 tests): empty state, scan triggers, stop scan, device list rendering, connect/disconnect actions, disabled states.
     - `ClockSyncPanel` (7 tests): live clock, 12h/24h toggle, DST toggle, manual sync disabled when disconnected, manual sync trigger when connected, progress bar, last synced timestamp.
     - `MockWatchPreview` (3 tests): Casio F-91W bezel and LCD, simulated register reflection, 12h AM/PM mode.
     - `App Full Integration Workflow` (4 tests): layout rendering, driver toggle switching, error banner display and clearing, and full end-to-end user flow (scan -> connect -> manual sync -> verify LCD updated -> disconnect).

### 1.3 Verification Command Outputs
1. `npm test`:
   - 9 test files executed (`serialization.test.ts`, `syncService.test.ts`, `mockBleService.test.ts`, `stateMachine.test.ts`, `challenge_m3.test.ts`, `smoke.test.ts`, `uiComponents.test.tsx`, `challenge_m1.test.ts`, `challenge_m2.test.ts`).
   - 193 total tests executed, 193 passed (100% pass rate).
2. `npm run typecheck`:
   - `tsc --noEmit` exited with code 0 (zero diagnostic errors).
3. `npm run build`:
   - `tsc && vite build` built production bundle in 342ms with zero errors.

---

## 2. Logic Chain

1. **Component Decoupling & Reactive Integration**:
   - Observation 1.1 requires the companion UI to reflect live connection state, handle scanning and manual sync, and toggle between hardware and simulated drivers.
   - Milestone 3 established `useBleConnection`, which encapsulates the 6-state FSM, GATT sync pipeline, and BLE HAL.
   - In `App.tsx`, `useBleConnection` is bound at the top level and distributes state and memoized callbacks down to `ConnectionStatusBadge`, `DeviceDiscovery`, and `ClockSyncPanel`.
   - `MockWatchPreview` directly consumes `bleClient` to inspect virtual watch hardware registers without polluting application state with simulation-specific data.

2. **Mobile Usability & Feedback Precision**:
   - In mobile BLE usage, physical GATT writes can fail or stall if unconfirmed.
   - `ClockSyncPanel` enforces that the manual sync button is disabled when `status !== 'CONNECTED'`. When clicked, it provides instant loading feedback, animates a multi-step progress bar during the sequential write chain, and updates the "Last Synced" timestamp upon success.
   - `DeviceDiscovery` parses RSSI into 4 intuitive signal quality bands (Excellent, Good, Fair, Weak) with dBm readouts, preventing user confusion when connecting.

3. **Authentic Hardware Simulation Preview**:
   - Per Observation 1.1, `MockWatchPreview` models an authentic Casio F-91W watch face.
   - When using `MockBleService`, the preview polls `getWatchState()` every 500ms, immediately updating whenever `syncClock` writes new time, timezone, format mode, or DST flags to the virtual watch GATT database.
   - This provides immediate visual confirmation to developers and testers in non-hardware environments that the full GATT serialization and write pipeline succeeded.

4. **Backward Compatibility & Regression Prevention**:
   - Milestone 1 tests (`tests/smoke.test.ts` and `tests/challenge_m1.test.ts`) assert on specific DOM text (`'F91_Jepler'`, `'Smartwatch Companion'`, `'Ready for Discovery'`, `'Disconnected'`, `<code>fa35b2f0...</code>`).
   - All components were designed to satisfy these contract strings while presenting an elevated, modern retro Casio aesthetic.
   - Result: All 166 prior tests continue to pass 100% without modification, alongside the 27 new tests.

---

## 3. Caveats

- In `MockWatchPreview.tsx`, when connected to `CapacitorBleService` (live mobile hardware), raw GATT register inspection is not available over BLE read without active notifications enabled on the Zephyr firmware. The preview reflects the driver status accordingly ("Hardware Driver").
- Vitest executes in a jsdom environment where timer-based tick animations run deterministically; testing manual sync uses React Testing Library's `act` and `waitFor` to verify async state transitions.

---

## 4. Conclusion

Milestone 4 (User Interface & Visual Synchronization Panel) is fully implemented, verified, and complete:
- Built `ConnectionStatusBadge`, `DeviceDiscovery`, `ClockSyncPanel`, `MockWatchPreview`, `App.tsx`, and `App.css` fulfilling requirement R4 and all acceptance criteria.
- Added 27 new React Testing Library unit and integration tests in `tests/uiComponents.test.tsx`.
- 100% automated test pass rate across the full project test suite (193/193 tests passing).
- Zero TypeScript typecheck errors and production build completes cleanly.

---

## 5. Verification Method

To independently verify Milestone 4:

1. **Execute All Test Suites**:
   ```bash
   cd /Users/jacobloesch/Documents/F91_Jepler/Software/companion_app
   npm test
   ```
   *Expected Result*: All 9 test files pass with 193/193 passing tests (100% pass rate).

2. **Execute TypeScript Strict Typecheck**:
   ```bash
   cd /Users/jacobloesch/Documents/F91_Jepler/Software/companion_app
   npm run typecheck
   ```
   *Expected Result*: Exits with code 0 and zero errors.

3. **Execute Production Vite Build**:
   ```bash
   cd /Users/jacobloesch/Documents/F91_Jepler/Software/companion_app
   npm run build
   ```
   *Expected Result*: Exits with code 0, bundling clean assets into `dist/`.
