jacobl423/F91_Jepler/.agents/teamwork/worker_m4/progress.md

# Progress Log — Milestone 4 (Worker 4)

Last visited: 2026-10-05T04:34:30Z
Current state: Implementation and verification complete

## Completed Steps
- Read DISPATCH.md, ORIGINAL_REQUEST.md, PROJECT.md, and worker_m3/handoff.md.
- Created BRIEFING.md and local skill reference for modern web development.
- Implemented `src/components/ConnectionStatusBadge.tsx`: live badge for all 6 connection states with device ID and RSSI.
- Implemented `src/components/DeviceDiscovery.tsx`: scanning controls, discovered devices list, signal strength meters, connect/disconnect triggers.
- Implemented `src/components/ClockSyncPanel.tsx`: real-time digital system clock, timezone offset calculation, 12h/24h toggle, DST toggle, dedicated manual sync button, GATT progress bar, and "Last Synced" timestamp.
- Implemented `src/components/MockWatchPreview.tsx`: authentic Casio F-91W LCD digital screen reflecting simulated watch registers and link status.
- Implemented `src/App.tsx` and `src/App.css`: responsive mobile container, driver selector between Simulated Watch and Hardware BLE, dismissible error alerts, safe area padding, and retro-modern styling.
- Created `tests/uiComponents.test.tsx`: 27 comprehensive React Testing Library component and integration tests.
- Verified test suite: `npm test` runs 193/193 tests passing (100% pass rate).
- Verified typechecking: `npm run typecheck` exits with code 0.
- Verified build: `npm run build` completes production bundle in 342ms.

## Next Steps
- Write handoff report `worker_m4/handoff.md`.
- Send completion message to parent orchestrator agent.
