jacobl423/F91_Jepler/.agents/teamwork/worker_m6/BRIEFING.md

# BRIEFING — 2026-10-05T05:18:30Z

## Mission
Build and verify the sideloadable Android APK (`app-debug.apk`) for the F91_Jepler companion app and document comprehensive sideloading procedures.

## 🔒 My Identity
- Archetype: worker
- Roles: implementer, qa, specialist
- Working directory: /Users/jacobloesch/Documents/F91_Jepler/.agents/teamwork/worker_m6
- Original parent: 73b327f6-797d-4e99-bde6-8417a8908ff9
- Milestone: M6: Sideloadable Android APK Build & Verification

## 🔒 Key Constraints
- OpenJDK 21 LTS at `/Users/jacobloesch/Library/Application Support/minecraft/runtime/java-runtime-delta/mac-os-arm64/java-runtime-delta/jre.bundle/Contents/Home`
- Android SDK at `/Users/jacobloesch/Library/Android/sdk`
- Build tools at `$ANDROID_HOME/build-tools/35.0.0` and platform-tools at `$ANDROID_HOME/platform-tools`
- Ensure App.tsx initializes to hardware BLE mode if `Capacitor.isNativePlatform()` is true while keeping simulation toggle available.
- All existing 325 unit/integration tests must pass cleanly.
- Verify APK using file, unzip, aapt, zipalign, and apksigner.
- Generate top-level copy at `Software/companion_app/F91_Jepler-companion-debug.apk`.
- Comprehensive sideloading instructions (ADB and direct transfer/installer).
- Genuine implementation with no dummy outputs.

## Current Parent
- Conversation ID: 73b327f6-797d-4e99-bde6-8417a8908ff9
- Updated: 2026-10-05T05:18:30Z

## Task Summary
- **What to build**: Production Android APK build (`assembleDebug`), hardware mode auto-detection on native Capacitor platform, artifact validation, copy to companion app root, and sideloading documentation.
- **Success criteria**:
  1. `App.tsx` initializes to hardware BLE mode when `Capacitor.isNativePlatform()` is true; toggle remains available.
  2. `npm test` passes 100% (327/327 tests).
  3. `npm run build` and `npx cap sync android` succeed.
  4. `./gradlew assembleDebug` completes with BUILD SUCCESSFUL using JDK 21 and Android SDK 35.
  5. APK verified via file, unzip, aapt, zipalign, apksigner.
  6. APK copied to `Software/companion_app/F91_Jepler-companion-debug.apk`.
  7. Detailed sideloading instructions documented.
- **Interface contracts**: `/Users/jacobloesch/Documents/F91_Jepler/.agents/teamwork/orchestrator_apk/SCOPE.md`
- **Code layout**: `/Users/jacobloesch/Documents/F91_Jepler/.agents/teamwork/PROJECT.md`

## Key Decisions Made
- Updated `App.tsx` so `driverMode` and `useBleConnection` initialize with `CapacitorBleService` when `Capacitor.isNativePlatform()` is true and no `clientOverride` is supplied.
- Added 2 new unit tests in `tests/uiComponents.test.tsx` checking driver default mode in native vs non-native environments. Total test count increased from 325 to 327 (all passing).
- Copied debug APK to top-level `Software/companion_app/F91_Jepler-companion-debug.apk` (4,314,108 bytes).
- Verified APK alignment (4-byte zipalign OK) and v2 signature scheme (apksigner verified OK).

## Artifact Index
- `Software/companion_app/src/App.tsx` — Native platform BLE hardware auto-selection
- `Software/companion_app/tests/uiComponents.test.tsx` — Unit tests for driver initialization
- `Software/companion_app/android/app/build/outputs/apk/debug/app-debug.apk` — Output debug APK
- `Software/companion_app/F91_Jepler-companion-debug.apk` — User-accessible debug APK copy (4.3 MB)
- `/Users/jacobloesch/Documents/F91_Jepler/.agents/teamwork/worker_m6/handoff.md` — Handoff report

## Change Tracker
- **Files modified**:
  - `Software/companion_app/src/App.tsx`: Auto-initialize to hardware BLE mode if `Capacitor.isNativePlatform()` is true.
  - `Software/companion_app/tests/uiComponents.test.tsx`: Added 2 unit tests covering native and web default driver selection.
  - `Software/companion_app/F91_Jepler-companion-debug.apk`: Placed verified APK copy for user convenience.
- **Build status**: PASS (Vite build, Capacitor sync, Gradle assembleDebug all succeeded)
- **Pending issues**: None

## Quality Status
- **Build/test result**: PASS (327/327 tests passing)
- **Lint status**: 0 errors (TypeScript strict check clean)
- **Tests added/modified**: 2 tests added for native platform driver initialization

## Loaded Skills
- None explicitly assigned
