jacobl423/F91_Jepler/.agents/teamwork/worker_m6/progress.md

# Progress Tracker — Milestone M6

Last visited: 2026-10-05T05:18:00Z

- [x] Initialized DISPATCH.md and BRIEFING.md
- [x] Inspect App.tsx and update BLE driver initialization for native platforms (Capacitor.isNativePlatform())
- [x] Add tests for native platform driver initialization in `tests/uiComponents.test.tsx`
- [x] Run test suite (`npm test`) in `Software/companion_app` (all 327 tests passing)
- [x] Run web build (`npm run build`)
- [x] Run Capacitor sync (`npx cap sync android`)
- [x] Run Gradle assembleDebug (`./gradlew assembleDebug` with OpenJDK 21 and Android SDK 35)
- [x] Copy APK to `Software/companion_app/F91_Jepler-companion-debug.apk`
- [x] Verify APK with Android SDK tools (`file`, `unzip`, `aapt`, `zipalign`, `apksigner`)
- [x] Write detailed sideloading instructions and handoff report
