jacobl423/F91_Jepler/.agents/teamwork/worker_m4/skills/modern-web-guidance.md

# Modern Web Guidance (Worker 4 Skill Reference)

Search tool for modern web development best practices.
- Trigger immediately for: UI/Layout, Frameworks, General Frontend, Modern CSS/HTML.
- Follow baseline widely available standards, clean responsive layout, accessible contrast, accessible touch targets, and robust component architecture.
