jacobl423/F91_Jepler/.agents/teamwork/auditor_m2_1/progress.md

# Progress — Forensic Auditor M2-1

Last visited: 2026-10-05T21:35:10Z

## Current Status
- Completed forensic integrity audit of Milestone 2.
- Verified genuine implementation, zero facades, clean `swift build`, and full wiring.
- Verdict: CLEAN. Writing handoff.md.

## Checklist
- [x] Step 1: Record dispatch and initialize BRIEFING / progress tracking
- [x] Step 2: Source Code Analysis & Inspection of Milestone 2 files
  - [x] Inspect `ProjectSidebarView.swift`
  - [x] Inspect `ContentView.swift`
  - [x] Inspect `KeyboardMonitor.swift`
  - [x] Inspect `SessionAsset.swift`
  - [x] Inspect `EmulatorSession.swift` & related integration points
- [x] Step 3: Hardcoded output & Facade detection
  - [x] Check for dummy closures, empty stubs, fake dropzones
  - [x] Check for hardcoded test results or bypasses
- [x] Step 4: Behavioral verification
  - [x] Run `swift build` in `Software/macOS_App` (Exit code 0, 0 errors)
  - [x] Run unit tests / verification scripts
- [x] Step 5: Adversarial stress test & wiring check
  - [x] Verify dropzone handlers genuinely update `EmulatorSession`
  - [x] Verify keyboard shortcut handling does not clash with watch keyboard monitoring
  - [x] Verify split view configuration and non-modal quick action menus
- [x] Step 6: Mode-Specific Flagging (Phase 2: Development Mode CLEAN)
- [x] Step 7: Final handoff report & verdict
