jacobl423/F91_Jepler/.agents/teamwork/auditor_m3/BRIEFING.md

# BRIEFING — 2026-10-05T04:22:00Z

## Mission
Forensic integrity audit of Milestone 3: State Machine & Sequential Sync Service in companion app.

## 🔒 My Identity
- Archetype: forensic_auditor
- Roles: critic, specialist, auditor
- Working directory: /Users/jacobloesch/Documents/F91_Jepler/.agents/teamwork/auditor_m3
- Original parent: 597ea6c0-a703-4980-a746-5cc67a9a63e2
- Target: Milestone 3 (State Machine & Sequential Sync Service)

## 🔒 Key Constraints
- Audit-only — do NOT modify implementation code
- Trust NOTHING — verify everything independently
- Adhere strictly to ORIGINAL_REQUEST.md ground-truth constraints
- Run npm test, npm run typecheck, and npm run build directly
- Issue explicit verdict: CLEAN or INTEGRITY VIOLATION

## Current Parent
- Conversation ID: 597ea6c0-a703-4980-a746-5cc67a9a63e2
- Updated: 2026-10-05T04:17:40Z

## Audit Scope
- **Work product**: Software/companion_app (connectionStateMachine.ts, syncService.ts, useBleConnection.ts, test suite)
- **Profile loaded**: General Project
- **Audit type**: forensic integrity check

## Audit Progress
- **Phase**: reporting
- **Checks completed**: [Ground truth analysis, Pre-populated artifact scan, Source code analysis for facades/hardcoded results, Empirical test suite execution (npm test), TypeScript typecheck (npm run typecheck), Production build (npm run build), Adversarial stress testing (challenge_m3.test.ts), Layout compliance check]
- **Checks remaining**: []
- **Findings so far**: CLEAN — zero integrity violations, robust sequential GATT pipeline, genuine state machine.

## Key Decisions Made
- Confirmed mode is Development per ORIGINAL_REQUEST.md line 8.
- Developed 18-test adversarial stress suite (tests/challenge_m3.test.ts) probing mid-sync drops, timeouts, GATT ATT errors, burst discovery packets, and extreme timezone offsets.

## Artifact Index
- /Users/jacobloesch/Documents/F91_Jepler/.agents/teamwork/auditor_m3/DISPATCH.md — Dispatch log
- /Users/jacobloesch/Documents/F91_Jepler/.agents/teamwork/auditor_m3/BRIEFING.md — Situational awareness
- /Users/jacobloesch/Documents/F91_Jepler/.agents/teamwork/auditor_m3/progress.md — Liveness & progress tracking
- /Users/jacobloesch/Documents/F91_Jepler/.agents/teamwork/auditor_m3/handoff.md — Final audit report
- /Users/jacobloesch/Documents/F91_Jepler/Software/companion_app/tests/challenge_m3.test.ts — Adversarial audit stress suite

## Attack Surface
- **Hypotheses tested**:
  - H1: State machine survives unexpected link drops across all 6 states without unhandled exceptions (PASS)
  - H2: Clock sync executes writes strictly sequentially and aborts mid-sync if disconnected (PASS)
  - H3: Step timeouts and GATT errors are caught cleanly and mapped to typed errors (PASS)
  - H4: Extreme timezone offsets (-720m to +840m) serialize into correct 2's complement byte layouts (PASS)
  - H5: High-frequency burst scanning (1,000 packets) deduplicates cleanly without memory leakage (PASS)
- **Vulnerabilities found**: None in production codebase.
- **Untested angles**: Hardware BLE interactions with physical nRF52 chip (covered by native Capacitor plugin on physical device).

## Loaded Skills
- None
