jacobl423/F91_Jepler/.agents/teamwork/auditor_m3/handoff.md

# Forensic Audit Report: Milestone 3 — State Machine & Sequential Sync Service

**Auditor**: Forensic Auditor M3  
**Target**: Milestone 3 (`Software/companion_app`)  
**Integrity Mode**: Development (per `ORIGINAL_REQUEST.md`)  
**Verdict**: **CLEAN**  
**Timestamp**: 2026-10-05T04:22:30Z  

---

## 1. Observation

### 1.1 Integrity Forensics & Code Analysis
Direct empirical inspection was conducted across all files created/modified for Milestone 3:
- **`src/state/connectionStateMachine.ts`** (551 lines):
  - Canonical 6-state definition (`DISCONNECTED`, `SCANNING`, `CONNECTING`, `CONNECTED`, `SYNCING`, `ERROR`).
  - 11 typed transition actions (`START_SCAN`, `STOP_SCAN`, `DEVICE_FOUND`, `SELECT_DEVICE`, `CONNECT_SUCCESS`, `CONNECT_FAILURE`, `DISCONNECT`, `START_SYNC`, `SYNC_SUCCESS`, `SYNC_FAILURE`, `CLEAR_ERROR`).
  - Strict transition permissions matrix `VALID_TRANSITIONS` guaranteeing `DISCONNECT` is handled cleanly from all 6 states.
  - Pure, immutable reducer `connectionReducer` with optional strict mode throwing `InvalidTransitionError`.
  - Object-oriented `ConnectionStateMachine` managing listener subscriptions and error isolation.
  - Zero hardcoded test return values, zero facade implementations, zero stubbed functions.
- **`src/state/syncService.ts`** (449 lines):
  - Strictly ordered 4-phase sequential write pipeline:
    1. Write Time (4 bytes LE uint32) -> await ACK
    2. Write Timezone (2 bytes LE int16) -> await ACK
    3. Write TimeMode (1 byte uint8) -> await ACK
    4. Write DST (1 byte uint8) -> await ACK
  - Link liveness validation (`verifyLinkAlive`) executed before and after each write step.
  - Temporary `onDisconnect` listener registered to catch unexpected link drop mid-sync and reject immediately with `SyncDisconnectedError`.
  - Timeout enforcement (`withTimeout`) mapping hung requests to typed `SyncTimeoutError`.
  - Underlying GATT write errors mapped to typed `SyncGattError`.
  - Proper listener cleanup in `finally` block preventing memory leaks.
- **`src/state/useBleConnection.ts`** (358 lines):
  - React 19 hook integrating `useReducer(connectionReducer)`.
  - Seamless HAL runtime switching between `MockBleService` and `CapacitorBleService`.
  - Automatic scan timeout cleanup, in-place peripheral deduplication with RSSI updates.
  - Mid-sync disconnect error routing (`SyncDisconnectedError` -> `DISCONNECTED`, GATT error -> `CONNECTED` with error state).

### 1.2 Pre-Populated Artifact & Facade Scan
- Artifact scan for pre-populated logs/results:
  `find . -maxdepth 3 -name '*.log' -o -name '*result*' -o -name '*output*'` returned only dependencies in `node_modules/`.
- Grep searches for `PASS`, `TODO`, `FIXME`, `NotImplemented`, or mock IDs in `src/` returned zero suspicious occurrences.
- Layout compliance verified: `.agents/teamwork/` contains zero code or test files.

### 1.3 Independent Test & Adversarial Verification Execution
1. **Existing Test Suite (`npm test`)**:
   - 7 test files, 148 tests passing (100%).
2. **Adversarial Stress Suite (`tests/challenge_m3.test.ts`)**:
   - Authored 18 exhaustive stress tests covering:
     - Mid-sync disconnections during write of Time, Timezone, Time Mode, and DST.
     - Timeout handling for hung writes on each characteristic.
     - GATT ATT write rejections across all 4 steps.
     - Extreme timezone offsets (Baker Island UTC-12:00 / -720m, Kiritimati UTC+14:00 / +840m, Adelaide UTC+9:30 / +570m).
     - Far-future timestamps (e.g. 2099-12-31).
     - High-frequency burst scanning (1,000 discovery packets across 3 alternating devices).
     - Rapid state machine transition bursts (12 consecutive event cycles).
     - Reducer snapshot immutability verification.
   - Result: 8 test files, 166 tests executed, 166 passed (100% pass rate).
3. **TypeScript Strict Typecheck (`npm run typecheck`)**:
   - `tsc --noEmit` exited with code 0 (zero diagnostic errors).
4. **Vite Production Build (`npm run build`)**:
   - `tsc && vite build` built client bundle in 248ms with zero errors.

---

## 2. Logic Chain

1. **State Machine Invariant Verification**:
   - Observation 1.1 reveals a formal transition matrix `VALID_TRANSITIONS` covering all 6 states.
   - Requirement R2 mandates: "disconnection events update UI status cleanly without throwing unhandled exceptions".
   - The matrix explicitly permits `DISCONNECT` from all 6 states (`DISCONNECTED`, `SCANNING`, `CONNECTING`, `CONNECTED`, `SYNCING`, `ERROR`).
   - Testing confirmed that `DISCONNECT` resets selected peripheral state and transitions cleanly to `DISCONNECTED` with optional error messaging, satisfying R2 without throwing.
   - Illegal transitions in strict mode (e.g., initiating sync from `DISCONNECTED`) correctly throw `InvalidTransitionError`, preventing corrupt state states.

2. **Sequential GATT Write Authenticity**:
   - Zephyr RTOS `clock_service.c` strictly enforces ATT write offsets and lengths, expecting sequentially acknowledged writes.
   - In `syncService.ts`, all four GATT writes are awaited sequentially in the exact specified order: Time (4B LE) -> Timezone (2B LE) -> TimeMode (1B) -> DST (1B).
   - If a mid-sync disconnect occurs, the active disconnect listener and `verifyLinkAlive` guard halt execution immediately, preventing subsequent dangling writes.
   - All payloads are serialized using genuine Little-Endian byte serializers and validated against the simulated GATT database in `MockBleService`.

3. **Integrity Mode Conformance**:
   - Under Development Mode (per `ORIGINAL_REQUEST.md`), prohibited patterns are hardcoded test results, facade implementations, and fabricated verification outputs.
   - The implementation was found to be fully authentic: real logic, genuine mathematical byte conversions, full reactive React integration, and zero facades.

---

## 3. Caveats

- One deliberate test in `tests/stateMachine.test.ts` (SM-7) verifies that if an external subscriber listener throws an exception, the state machine isolates the exception and logs an error to stderr without interrupting state transitions. The resulting error output in stderr during test execution is expected and confirms error isolation.
- Hardware BLE execution relies on `@capacitor-community/bluetooth-le` when deployed on physical iOS/Android devices. Unit and integration tests verify the protocol logic via `MockBleService`.

---

## 4. Conclusion

**Verdict**: **CLEAN**

Milestone 3 (State Machine & Sequential Sync Service) fully complies with all specifications and integrity standards:
- Finite state machine correctly enforces 6 states and 11 transitions.
- Sequential clock sync pipeline executes genuine GATT writes in exact sequence with full disconnect, timeout, and GATT error guards.
- React integration hook `useBleConnection` provides complete reactive bindings and runtime BLE driver interchangeability.
- 166/166 automated tests pass (including 18 adversarial stress tests).
- Typecheck and production bundle builds pass with zero errors.

---

## 5. Verification Method

To independently verify this audit:

```bash
cd /Users/jacobloesch/Documents/F91_Jepler/Software/companion_app

# 1. Run full Vitest test suite (includes 18 adversarial stress tests)
npm test

# 2. Run TypeScript strict typecheck
npm run typecheck

# 3. Run production Vite build
npm run build
```

Expected output:
- `npm test`: 8 test files passed, 166 tests passed (100% pass rate).
- `npm run typecheck`: Exit code 0, 0 errors.
- `npm run build`: Exit code 0, bundle generated in `dist/`.
