jacobl423/F91_Jepler/.agents/teamwork/auditor_m4/BRIEFING.md

# BRIEFING — 2026-10-05T04:40:00Z

## Mission
Forensic integrity audit of Milestone 4 (User Interface & Visual Synchronization Panel) in Software/companion_app

## 🔒 My Identity
- Archetype: forensic_auditor
- Roles: critic, specialist, auditor
- Working directory: /Users/jacobloesch/Documents/F91_Jepler/.agents/teamwork/auditor_m4
- Original parent: 597ea6c0-a703-4980-a746-5cc67a9a63e2
- Target: Milestone 4 (User Interface & Visual Synchronization Panel)

## 🔒 Key Constraints
- Audit-only — do NOT modify implementation code
- Trust NOTHING — verify everything independently
- Integrity Mode: development (per ORIGINAL_REQUEST.md line 8)
- Ground-truth user constraints from ORIGINAL_REQUEST.md always take precedence

## Current Parent
- Conversation ID: 597ea6c0-a703-4980-a746-5cc67a9a63e2
- Updated: not yet

## Audit Scope
- **Work product**: Software/companion_app UI components (ConnectionStatusBadge.tsx, DeviceDiscovery.tsx, ClockSyncPanel.tsx, MockWatchPreview.tsx, App.tsx, App.css), tests/uiComponents.test.tsx, and tests/challenge_m4.test.tsx
- **Profile loaded**: General Project
- **Audit type**: forensic integrity check

## Audit Progress
- **Phase**: reporting
- **Checks completed**:
  - Phase 1 Source Code Analysis (hardcoded output detection, facade detection, pre-populated artifact scan)
  - Phase 2 Behavioral Verification (`npm test` 223/223 pass, `npm run typecheck` 0 errors, `npm run build` clean bundle in 343ms)
  - Adversarial Review & Stress Suite (30 tests in tests/challenge_m4.test.tsx)
- **Checks remaining**: None
- **Findings so far**: CLEAN (Zero integrity violations found)

## Attack Surface
- **Hypotheses tested**:
  - H1: UI buttons use fake click handlers or stubs -> REFUTED (tested real event dispatches)
  - H2: ClockSyncPanel hardcodes time or tz -> REFUTED (tested dynamic clock ticks & tz calculation)
  - H3: MockWatchPreview displays hardcoded LCD digits -> REFUTED (tested midnight, noon, leap day, register synchronization)
  - H4: Rapid click bursts or extreme RSSI crash components -> REFUTED (passed 25-click bursts and extreme RSSI)
  - H5: Component unmount leaks timer intervals -> REFUTED (passed 50 unmount cycles cleanly)
- **Vulnerabilities found**: None
- **Untested angles**: Hardware BLE execution on physical silicon (requires physical mobile device with Zephyr watch)

## Loaded Skills
- None

## Key Decisions Made
- Prioritized ORIGINAL_REQUEST.md integrity mode ("development") while running mode-agnostic Phase 1 checks
- Authored independent adversarial stress test suite in `tests/challenge_m4.test.tsx` (30 tests)

## Artifact Index
- DISPATCH.md — audit assignment
- BRIEFING.md — persistent situational awareness
- progress.md — liveness heartbeat
- handoff.md — final audit report
