jacobl423/F91_Jepler/.agents/teamwork/auditor_m4/progress.md

# Progress — Forensic Auditor M4

**Last visited**: 2026-10-05T04:40:15Z  
**Status**: Audit complete — Verdict: CLEAN  

### Progress Checklist
- [x] Received dispatch and recorded in DISPATCH.md
- [x] Initialized BRIEFING.md and progress.md
- [x] Inspect source code of all M4 deliverables in `Software/companion_app`
  - [x] `src/components/ConnectionStatusBadge.tsx`
  - [x] `src/components/DeviceDiscovery.tsx`
  - [x] `src/components/ClockSyncPanel.tsx`
  - [x] `src/components/MockWatchPreview.tsx`
  - [x] `src/App.tsx`
  - [x] `src/App.css`
  - [x] `tests/uiComponents.test.tsx`
- [x] Phase 1 Forensic Checks:
  - [x] Hardcoded output detection: PASS (dynamic state-driven rendering)
  - [x] Facade detection: PASS (authentic event handling, genuine React hooks)
  - [x] Pre-populated artifact detection: PASS (0 pre-populated logs/results outside node_modules)
- [x] Phase 2 Behavioral Verification:
  - [x] Run `npm test`: PASS (10 suites, 223/223 tests passing)
  - [x] Run `npm run typecheck`: PASS (`tsc --noEmit` exited code 0)
  - [x] Run `npm run build`: PASS (`tsc && vite build` built in 343ms)
  - [x] Output & state reactivity verification: PASS (end-to-end full user flow verified)
- [x] Adversarial Review & Edge Case Stress-Testing: PASS (`tests/challenge_m4.test.tsx`, 30/30 passing)
- [x] Complete BRIEFING.md and generate handoff.md with explicit verdict: CLEAN
