jacobl423/F91_Jepler/.agents/teamwork/auditor_m6/progress.md

# Progress Log — Forensic Auditor M6

Last visited: 2026-10-05T15:44:20Z

## Status: Reporting
- Completed Phase 1 Source code & diff forensics: clean, genuine code in `App.tsx`, `gattSerializer.ts`, `capacitorBleService.ts`.
- Completed Phase 1 Build pipeline & timestamp analysis: APK timestamp 00:16:17 2026, convenience copy 00:16:23 2026. SHA-256 hashes match.
- Completed Phase 1 Binary artifact forensics:
  * 8 DEX slices decompiled with `dexdump`, verified Dalvik 037 bytecode.
  * Verified classes: `MainActivity`, `CapacitorBridge`, `BluetoothLe` (902 occurrences in classes2.dex).
  * Web asset packaging: exact SHA-256 match between `dist/` and `assets/public/` inside the APK.
  * Zip alignment: `zipalign -c -v 4` passed (returncode 0).
  * Cryptographic signature: `apksigner verify` confirms APK Signature Scheme v2; certificate matches host `~/.android/debug.keystore` (SHA256: 32:6E:20:17:4A:4E:6C:72:A4:7C:77:7E:04:0E:FC:A1:94:7E:8B:3A:96:1E:B1:95:72:F4:34:52:66:3A:F7:8F).
- Completed Phase 1 Independent build & test execution:
  * `npm test`: 11 test suites, 327 tests passed cleanly in 1.36s.
  * `npm run typecheck`: clean (0 errors).
  * `./gradlew assembleDebug`: 154 tasks up-to-date, BUILD SUCCESSFUL.
- Completed Phase 2 Mode-specific flagging (Development mode):
  * No hardcoded test outputs.
  * No facade implementations.
  * No pre-fabricated or mock artifacts.
- Completed Adversarial Challenge & Stress-Testing.
- Now drafting final handoff report `handoff.md`.
