jacobl423/F91_Jepler/.agents/teamwork/challenger_m1_1/DISPATCH.md

# Dispatch for Challenger M1_1

## Identity
- Role: Binary Header & Inspector Challenger
- Type: teamwork_preview_challenger
- Working directory: /Users/jacobloesch/Documents/F91_Jepler/.agents/teamwork/challenger_m1_1
- Parent Orchestrator: /Users/jacobloesch/Documents/F91_Jepler/.agents/teamwork/orchestrator_macos
- Authoritative User Request: /Users/jacobloesch/Documents/F91_Jepler/.agents/teamwork/ORIGINAL_REQUEST.md
- Project Scope Document: /Users/jacobloesch/Documents/F91_Jepler/.agents/teamwork/orchestrator_macos/PROJECT.md

## Scope & Instructions
Empirically stress-test `AssetInspector.swift` and `SessionAsset.swift` in `Software/macOS_App`:
- Write test harnesses/scripts testing `AssetInspector.inspect`:
  1. Valid repository files: `app.signed.bin` (MCUboot), `mcuboot.elf` (ELF ARM Cortex-M), `f91_jepler.resc` (Renode script), `f91_jepler.kicad_pcb` (KiCad S-expr), `blaster_6810.hex` (Intel HEX).
  2. Edge cases and adversarial inputs:
     - 0-byte empty files
     - Corrupted headers (truncated ELF, invalid MCUboot magic)
     - Pseudo-hex text files (lines with colons that are not valid hex records)
     - Non-existent paths
     - Extremely large files or deep paths
- Verify no uncaught exceptions, hangs, or memory leaks occur.
- Deliver your verdict (CONFIRMED / APPROVE or REJECT) and empirical test results in `/Users/jacobloesch/Documents/F91_Jepler/.agents/teamwork/challenger_m1_1/handoff.md`.

## 2026-10-05T20:27:49Z
You are Challenger 1 for Milestone 1 of the F91_Jepler project.
Your working directory is /Users/jacobloesch/Documents/F91_Jepler/.agents/teamwork/challenger_m1_1.
Read /Users/jacobloesch/Documents/F91_Jepler/.agents/teamwork/ORIGINAL_REQUEST.md, /Users/jacobloesch/Documents/F91_Jepler/.agents/teamwork/orchestrator_macos/PROJECT.md, and /Users/jacobloesch/Documents/F91_Jepler/.agents/teamwork/challenger_m1_1/DISPATCH.md before starting work.
Empirically stress-test AssetInspector.swift and SessionAsset.swift against repository binaries (app.signed.bin, mcuboot.elf, f91_jepler.resc, f91_jepler.kicad_pcb, blaster_6810.hex) and adversarial inputs (0-byte files, corrupted headers, pseudo-hex lines, non-existent files).
Deliver your verdict (APPROVE or REJECT) and empirical test results in /Users/jacobloesch/Documents/F91_Jepler/.agents/teamwork/challenger_m1_1/handoff.md and report back when complete.
