jacobl423/F91_Jepler/.agents/teamwork/challenger_m1_2/handoff.md

# Handoff Report: Challenger M1_2 — Renode Script Generation & Emulator Session Persistence

**Verdict**: **APPROVE**

---

## 1. Observation

### Empirical Test Execution
An isolated test harness was compiled and executed against the `Software/macOS_App` codebase (macOS 13+, Apple Swift 5.9 toolchain) using the following compiler invocation:
```bash
swiftc -plugin-path /Applications/Xcode.app/Contents/Developer/Platforms/MacOSX.platform/Developer/usr/lib/swift/host/plugins \
  -parse-as-library $(find /Users/jacobloesch/Documents/F91_Jepler/Software/macOS_App/F91JeplerEmulator -name "*.swift" ! -name "App.swift") \
  /tmp/ChallengerM1Harness.swift -o /tmp/run_challenger_m1_2
```
The test harness executed 136 assertions across 8 distinct suites with zero failures:
```
==================================================
SUMMARY: 136 PASSED, 0 FAILED
==================================================
```

### Inspected Implementation Details

#### 1. RenodeScriptGenerator.swift
- **Dynamic Binary Format Handling** (`Lines 48–62`):
  ```swift
  public static func formatLoadCommand(
      variable: String,
      format: BinaryFormat,
      loadAddress: UInt32
  ) -> String {
      switch format {
      case .elf:
          return "sysbus LoadELF \(variable)"
      case .hex:
          return "sysbus LoadHEX \(variable)"
      case .binary:
          let addr = String(format: "0x%05x", loadAddress)
          return "sysbus LoadBinary \(variable) \(addr)"
      }
  }
  ```
- **Resc Generation & Reset Macro** (`Lines 105–124`):
  ```swift
  // Dynamically emit bootloader load command
  if let bl = bootloaderPath, !bl.isEmpty {
      let blFmt = bootloaderFormat ?? detectFormat(path: bl)
      let blCmd = formatLoadCommand(
          variable: "$mcuboot_bin",
          format: blFmt,
          loadAddress: bootloaderLoadAddress
      )
      script += "\n    \(blCmd)"
  }
  
  // Dynamically emit application load command
  let appFmt = appFormat ?? detectFormat(path: appBinPath)
  let appCmd = formatLoadCommand(
      variable: "$app_bin",
      format: appFmt,
      loadAddress: appLoadAddress
  )
  script += "\n    \(appCmd)"
  ```
- **Format Auto-Detection & Magic Bytes Priority** (`Lines 14–45`):
  - Correctly prioritizes ELF magic `[0x7F, 0x45, 0x4C, 0x46]` (`\x7fELF`) and Intel HEX ASCII `:` (`0x3A`) in the first 16 bytes.
  - Successfully detects ELF even if given a deceptive `.bin` extension.
  - Successfully detects Intel HEX even if given a deceptive `.bin` extension.
  - Handles case-insensitive extensions (`.ELF`, `.HEX`, `.BIN`), alternative extensions (`.axf`, `.ihex`), and unknown extensions (`.dat` falling back to `.binary`).

#### 2. EmulatorSession.swift & SessionAsset.swift
- **Layout & View Mode State Persistence** (`Lines 38–54, 234–256`):
  - `isSidebarVisible` uses reactive `didSet` persisting to `SessionPersistenceKeys.isSidebarVisible`. Restores defaults to `true` if unset.
  - `sidebarWidth` uses `didSet` persisting to `SessionPersistenceKeys.sidebarWidth`. Restores clamped between `[230, 380]`, resetting invalid values (< 230 or > 380) to default `280`.
  - `selectedViewMode` uses `didSet` persisting to `SessionPersistenceKeys.selectedViewMode`. Restores matching `ViewMode(rawValue:)` or case-insensitively, falling back to `.split` on invalid/unrecognized strings.
- **Missing File Scrubbing on Startup** (`Lines 262–284`):
  - In `loadInitialAssets()`, queries `userDefaults.string(forKey: kind.userDefaultsKey)`.
  - If the path does not exist on disk (`FileManager.default.fileExists(atPath:) == false`), calls `userDefaults.removeObject(forKey: kind.userDefaultsKey)` and falls back to `loadDefaultAsset(kind: kind)` with `isCustom == false`.
- **Backwards-Compatible Computed Properties** (`Lines 71–125`):
  - `customPCBURL`, `customAppBinURL`, `customBootloaderURL`, `customRescURL` implemented with `{ get set }`.
  - Getter: returns `assets[kind]?.fileURL` if `asset.isCustom == true`, else `nil`.
  - Setter: if non-nil, triggers `updateAsset(kind:url:)`; if `nil`, triggers `revertAssetToDefault(kind:)`.
  - Bidirectional mutation verified: changing computed property updates `assets[kind]` and `UserDefaults`; calling `updateAsset` updates computed property; calling `revertAssetToDefault` sets computed property to `nil`.

#### 3. Build Status
- Target: `Software/macOS_App`
- Command: `swift build`
- Output: Exited 0 with `Build complete!`.

---

## 2. Logic Chain

1. **Dynamic Script Generation Validation**:
   - *Observation*: `RenodeScriptGenerator.generateResc` was tested across all 9 combinations of `(appFormat, bootloaderFormat)` for `[.elf, .hex, .binary]`.
   - *Logic*: In every permutation, the bootloader command emitted the exact Renode directive (`sysbus LoadELF $mcuboot_bin`, `sysbus LoadHEX $mcuboot_bin`, or `sysbus LoadBinary $mcuboot_bin 0x00000`), and the application command emitted `sysbus LoadELF $app_bin`, `sysbus LoadHEX $app_bin`, or `sysbus LoadBinary $app_bin 0x0c000`.
   - *Conclusion*: Dynamic command formatting strictly fulfills feature requirement #9 of `PROJECT.md`.

2. **Edge Cases and Address Formatting**:
   - *Observation*: Tested `bootloaderPath: nil` and `bootloaderPath: ""`, custom addresses (`0x26000`, `0x04000`), and boundaries (`0x00000`, `0xFFFFF`).
   - *Logic*: When bootloader is omitted or empty, no bootloader variables or load commands are generated. Custom addresses format with exact 5-hex-digit padding (`0x%05x`).

3. **Isolated Persistence & State Restoration**:
   - *Observation*: Tested with isolated `UserDefaults` suites (`test.suite.*`).
   - *Logic*: Modifications to `isSidebarVisible`, `sidebarWidth`, `selectedViewMode`, and asset paths were verified directly in the underlying `UserDefaults` dictionary. Instantiating fresh `EmulatorSession` instances with the same suite cleanly rehydrated all state.

4. **Missing Path Cleanup Resilience**:
   - *Observation*: Created custom assets, deleted application binary and PCB files from disk, and reinitialized `EmulatorSession(userDefaults: suite)`.
   - *Logic*: Stale keys for deleted files were scrubbed (`userDefaults.string` returned `nil`) and the corresponding assets reverted to `isCustom == false` (default embedded assets), while untouched files (`.bootloader`, `.rescScript`) remained custom.

5. **Backwards Compatibility**:
   - *Observation*: Exercised `customPCBURL`, `customAppBinURL`, `customBootloaderURL`, and `customRescURL` getters, setters, and `nil` assignments.
   - *Logic*: Existing UI bindings and legacy code paths remain completely functional without regressions.

---

## 3. Caveats

- **Async Metadata Inspection**: `AssetInspector.inspect` executes asynchronously in `Task.detached`. While `SessionAsset.fileURL` and `isCustom` are synchronously available upon session initialization, `metadata` and `.loaded` state populate on the main actor following header inspection completion (< 2ms for local SSD files).
- **Sandboxing Considerations**: Stored paths are raw POSIX strings in `UserDefaults`. If App Sandbox is enabled in later milestones, persistent paths will require security-scoped bookmarks (`bookmarkData(options:includingResourceValuesForKeys:relativeTo:)`). Under the current non-sandboxed configuration (`F91JeplerEmulator.entitlements`), direct filesystem paths are fully functional.

---

## 4. Conclusion

**Verdict: APPROVE**

The Milestone 1 work product meets and exceeds all requirements specified in `DISPATCH.md` and `PROJECT.md`:
1. `RenodeScriptGenerator.swift` correctly formats dynamic commands for all binary formats (`.elf`, `.hex`, `.bin`) and addresses.
2. `EmulatorSession.swift` provides robust, isolated `UserDefaults` state persistence, bounds clamping, and resilient missing-path scrubbing.
3. Backwards-compatible computed properties (`customPCBURL`, `customAppBinURL`, etc.) are fully synchronized with the underlying unified `assets` dictionary.
4. `swift build` in `Software/macOS_App` compiles cleanly with zero errors.

---

## 5. Verification Method

To independently verify the test suite:

### 1. Build Verification
```bash
cd /Users/jacobloesch/Documents/F91_Jepler/Software/macOS_App
swift build
```
*Expected Result*: Exits 0 with `Build complete!`.

### 2. Isolated Verification Command
Run the isolated verification harness directly against the repository sources:
```bash
cd /Users/jacobloesch/Documents/F91_Jepler
cat << 'EOF' > /tmp/verify_challenger_m1_2.swift
import Foundation

@main
struct Verifier {
    static func main() {
        let resc = RenodeScriptGenerator.generateResc(
            appBinPath: "/test/app.bin",
            bootloaderPath: "/test/boot.hex",
            uartLogPath: "/test/uart.log",
            appFormat: .binary,
            bootloaderFormat: .hex
        )
        assert(resc.contains("sysbus LoadHEX $mcuboot_bin"))
        assert(resc.contains("sysbus LoadBinary $app_bin 0x0c000"))
        
        let suite = UserDefaults(suiteName: "jepler.verify.\(UUID().uuidString)")!
        defer { suite.removePersistentDomain(forName: suite.name ?? "") }
        let session = EmulatorSession(userDefaults: suite)
        session.sidebarWidth = 333
        assert(suite.double(forKey: SessionPersistenceKeys.sidebarWidth) == 333)
        print("M1_2 INDEPENDENT VERIFICATION PASSED")
    }
}
EOF

swiftc -plugin-path /Applications/Xcode.app/Contents/Developer/Platforms/MacOSX.platform/Developer/usr/lib/swift/host/plugins \
  -parse-as-library $(find Software/macOS_App/F91JeplerEmulator -name "*.swift" ! -name "App.swift") \
  /tmp/verify_challenger_m1_2.swift -o /tmp/run_verify_m1_2
/tmp/run_verify_m1_2
rm -f /tmp/verify_challenger_m1_2.swift /tmp/run_verify_m1_2
```
*Expected Result*: Prints `M1_2 INDEPENDENT VERIFICATION PASSED` and exits 0.

### 3. Invalidation Conditions
- Any regression that causes `sidebarWidth` to accept values outside `[230, 380]` without reset.
- Modifying `SessionPersistenceKeys` strings, breaking state persistence across launches.
- Failure of `detectFormat` to fall back to raw binary when magic headers or extensions are unrecognized.
