jacobl423/F91_Jepler/.agents/teamwork/challenger_m1_2/progress.md

# Progress — Challenger M1-2

Last visited: 2026-10-05T20:35:10Z

## Status
Empirical stress testing complete. All 136 tests passed. Zero failures.

## Test Summary
- Suite 1: RenodeScriptGenerator 3x3 Format Matrix: 36 passed
- Suite 2: RenodeScriptGenerator Edge Cases & Custom Addresses: 10 passed
- Suite 3: Renode Format Detection (Magic Bytes & Extensions): 11 passed
- Suite 4: EmulatorSession UserDefaults State Persistence: 9 passed
- Suite 5: EmulatorSession Bounds Validation & Fallbacks: 6 passed
- Suite 6: EmulatorSession Missing File Cleanup & Scrubbing: 16 passed
- Suite 7: EmulatorSession Backwards Compatibility Bindings: 38 passed
- Suite 8: Advanced Edge Cases (missing file reloadAsset, empty path, batch reset): 10 passed
- Total: 136 / 136 PASSED (100% success rate).

## Current Step
Writing handoff.md and sending completion message to parent orchestrator.
