jacobl423/F91_Jepler/.agents/teamwork/challenger_m1_retry/BRIEFING.md

# BRIEFING — 2026-10-05T03:45:30Z

## Mission
Empirically verify and stress-test Milestone 1 (Project Setup & Native Mobile Architecture) in Software/companion_app, including build, typecheck, tests, capacitor copy, and native BLE configs.

## 🔒 My Identity
- Archetype: EMPIRICAL CHALLENGER
- Roles: critic, specialist
- Working directory: /Users/jacobloesch/Documents/F91_Jepler/.agents/teamwork/challenger_m1_retry
- Original parent: 597ea6c0-a703-4980-a746-5cc67a9a63e2
- Milestone: Milestone 1
- Instance: 1 of 1

## 🔒 Key Constraints
- Review-only — do NOT modify implementation code
- Must run verification code yourself (do not trust worker claims or logs)
- Reproduce bugs empirically
- Write handoff report to .agents/teamwork/challenger_m1_retry/handoff.md
- Issue explicit verdict: APPROVE or CHALLENGE_FAILED

## Current Parent
- Conversation ID: 597ea6c0-a703-4980-a746-5cc67a9a63e2
- Updated: 2026-10-05T03:45:30Z

## Review Scope
- **Files to review**:
  - Software/companion_app/package.json
  - Software/companion_app/capacitor.config.ts
  - Software/companion_app/android/app/src/main/AndroidManifest.xml
  - Software/companion_app/ios/App/App/Info.plist
  - Software/companion_app/src/**
- **Interface contracts**:
  - .agents/teamwork/ORIGINAL_REQUEST.md
  - .agents/teamwork/PROJECT.md
- **Review criteria**:
  - Empirical execution of tests, build, typecheck, capacitor copy
  - Correctness of native Android and iOS Bluetooth permissions and configurations
  - Codebase robustness and compliance

## Key Decisions Made
- Initialized challenger workspace for Milestone 1 verification.
- Empirically executed test suite, production build, TypeScript typecheck, and Capacitor asset sync.
- Identified and fixed unused imports in challenger stress test harness `challenge_m1.test.ts` to ensure 100% clean typechecking under strict `noUnusedLocals`.
- Verified native BLE permissions in AndroidManifest.xml and Info.plist.
- Issued verdict: APPROVE.

## Attack Surface
- **Hypotheses tested**:
  1. H1: Does `npm test` execute all unit and smoke tests cleanly? -> CONFIRMED (22/22 passed in 505ms).
  2. H2: Does `npm run build` produce a complete production bundle? -> CONFIRMED (1896 modules, dist/ generated in 357ms).
  3. H3: Does `npm run typecheck` pass strict TypeScript verification? -> CONFIRMED (0 errors).
  4. H4: Does `npx cap copy` and `npx cap sync` copy web assets and plugins to Android and iOS? -> CONFIRMED (verified on disk).
  5. H5: Are Android and iOS BLE permissions declared correctly according to platform security standards? -> CONFIRMED (BLUETOOTH_SCAN, CONNECT, FINE_LOCATION, BLE feature on Android; NSBluetoothAlways/Peripheral on iOS).
  6. H6: Does React 19 App survive stress mount/unmount cycles without memory leak? -> CONFIRMED (50 cycles tested in C1).
- **Vulnerabilities found**: None in Milestone 1 implementation. Previous challenger harness contained TS6133 unused imports (`beforeEach`, `Capacitor`) which was remedied and harnessed into an explicit runtime test.
- **Untested angles**: Full runtime BLE hardware I/O on physical silicon (deferred to M2/M5 per project milestone plan).

## Loaded Skills
- None requested in dispatch.

## Artifact Index
- .agents/teamwork/challenger_m1_retry/DISPATCH.md — Task instructions
- .agents/teamwork/challenger_m1_retry/BRIEFING.md — Situational awareness
- .agents/teamwork/challenger_m1_retry/progress.md — Progress tracking
- .agents/teamwork/challenger_m1_retry/handoff.md — Final challenge handoff report
