jacobl423/F91_Jepler/.agents/teamwork/challenger_m2_1/BRIEFING.md

# BRIEFING — 2026-10-05T21:40:00Z

## Mission
Empirically stress-test Milestone 2 dropzones, extension validation, metadata rendering, and KeyboardMonitor modifier isolation by writing and executing an empirical test harness, delivering a verifiable APPROVE/REJECT verdict.

## 🔒 My Identity
- Archetype: empirical_challenger
- Roles: critic, specialist
- Working directory: /Users/jacobloesch/Documents/F91_Jepler/.agents/teamwork/challenger_m2_1
- Original parent: 6b5ed2d8-2b1d-40f1-8ab6-ad53a69017cd
- Milestone: M2 (Collapsible Sidebar UI & Main Window Integration)
- Instance: 1 of 1

## 🔒 Key Constraints
- Review-only — do NOT modify implementation code in `Software/macOS_App/F91JeplerEmulator`
- `.agents/teamwork/` must contain only metadata — source, tests, or data there is a violation
- Empirical challenge: write and execute real test harnesses; do not rely on assumptions or claims
- Deliverable: handoff.md with 5 components (Observation, Logic Chain, Caveats, Conclusion, Verification Method) and APPROVE/REJECT verdict

## Current Parent
- Conversation ID: 6b5ed2d8-2b1d-40f1-8ab6-ad53a69017cd
- Updated: 2026-10-05T21:29:21Z

## Review Scope
- **Files to review**:
  - `Software/macOS_App/F91JeplerEmulator/Views/ProjectSidebarView.swift`
  - `Software/macOS_App/F91JeplerEmulator/Views/ContentView.swift`
  - `Software/macOS_App/F91JeplerEmulator/Views/AppTopBarView.swift`
  - `Software/macOS_App/F91JeplerEmulator/Utils/KeyboardMonitor.swift`
  - `Software/macOS_App/F91JeplerEmulator/Models/SessionAsset.swift`
  - `Software/macOS_App/F91JeplerEmulator/Models/EmulatorSession.swift`
  - `Software/macOS_App/F91JeplerEmulator/Engine/AssetInspector.swift`
- **Interface contracts**: PROJECT.md M2 specifications
- **Review criteria**:
  - Extension acceptance and rejection for all 4 asset kinds (`.pcb`, `.appFirmware`, `.bootloader`, `.rescScript`)
  - Rejection of invalid / spoofed extensions (`.png`, `.txt`, `.bin` on pcb, uppercase/mixed-case extensions, multiple dots)
  - Truncated path display and format badge computation
  - State transitions (empty, inspecting, loaded, error)
  - KeyboardMonitor modifier isolation: ensure raw `1`, `2`, `3` trigger callbacks, while `⌘0`, `⌘1`, `⌘2`, `⌥⌘S`, `^1`, etc. are passed through untouched and never swallowed
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
